daviddatuX25/Xentient/.planning/STATE.md

---
gsd_state_version: 1.0
milestone: v1.0
milestone_name: milestone
status: in_progress
last_updated: "2026-04-30T04:23:21.889Z"
progress:
  total_phases: 7
  completed_phases: 0
  total_plans: 0
  completed_plans: 0
---

# Project State: Xentient

## Project Reference

See: [.planning/PROJECT.md](file:///d:/Projects/Xentient/.planning/PROJECT.md) (updated 2026-04-19)

**Core value:** The IoT terminal — a thin voice/hardware bridge that lets any AI brain inhabit a physical room.
**Current focus:** Phase 8 (Web Console + Dashboard) COMPLETE — all 8 plans shipped. 203 tests passing, 0 TS errors. Dashboard served at localhost:3000 with Overview, Skill Manager, Telemetry, and Mode & Space panels.

## Active Context

Phase 1 (firmware), Phase 5 (docs), and Phase 6 (Xentient Layers) all complete. Platform Track P3 (ModeManager) and P4 (SpaceManager) built as part of Phase 6. CoreSkill types, SkillExecutor engine, SpaceManager, 8 MCP skill tools, observability notifications, core.ts wiring, and 34 Vitest tests — all committed and pushed.

Demo scope reduced: no furnished casing required — filming breadboard prototype as-is. P3-ASSY now covers breadboard assembly + validation only (no 3D-printed enclosure).

**Open bugs:** PIR wake not triggering ModeManager sleep→listen transition (9id, P0) — firmware ISR works, harness gap. Two P1 bugs deferred (bgx: dead MQTT sub, b94: audio prefix).

Quick task 260420-4do complete: ModeManager wired into Core runtime — MQTT mode/sensor events, idle timeouts (listen 60s, active 300s), PIR wake (sleep→listen), Pipeline mode-aware audio gating, LCD face display publishing on mode transitions.

## Milestone Status

| Milestone | Target Date | Status |
|---|---|---|
| V1 Prototype | 2026-04-24 | In Progress |

## Recent Decisions

- Bridge model adopted: Xentient = IoT terminal, not AI brain
- Three-tier architecture: Hardware / Core (Runtime + Web Control Panel) / AI Brain
- 4-layer doc system established (L0-L4)
- Phase 2 plans superseded by bridge reframe
- Two-track roadmap: Demo Track (frozen) + Platform Track (P1-P9)
- Brain Router: Core's dispatch layer routing handler calls across tiers
- Mem0 as primary memory layer (P2), Hermes as default brain (P1)
- Demo scope reduced: breadboard prototype filming, no furnished casing required
- P3-ASSY merged with 03-07: single hardware assembly task, breadboard scope only
- Phase 6 complete: CoreSkill types, SkillExecutor, SpaceManager, MCP tools, core wiring, 34 tests — all waves shipped
- Phase 7 planned: 6 gaps identified (G1-G6), 5 plans written (07-01 through 07-05), 5 design decisions locked
- Phase 1 confirmed complete: firmware (MQTT, LCD, mic, VAD, WS audio, camera relay, BME280, PIR ISR) all built and validated
- Platform Track P3/P4 already built as part of Phase 6 (ModeManager + SpaceManager)
- Roadmap + beads audited and aligned with actual project state
- Phase 8 added: Web Console + Dashboard — single-page HTML/JS dashboard served by ControlServer (NOT Laravel for v1), 8 plans (08-01 through 08-08)
- Phase 8 plan 07 complete: ControlServer refactored with MicroRouter route table, ControlServerDeps DI, 64KB body limit, static file fallthrough, SensorHistory ring buffer stub
- Phase 8 plan 01 complete: 16 REST endpoints (Skills 6, Packs 3, Spaces 2, Event Mappings 3, Sensor History 1, Config 1), PATCH allowlist, 409 conflict, 403 protected-delete, 32 tests
- PATCH allowlist: 9 patchable skill fields (enabled, displayName, trigger, actions, priority, cooldownMs, modeFilter, escalation, collect); forbidden: id, source, fireCount, escalationCount
- POST skill collision returns 409 (REST explicit), not MCP silent overwrite
- /api/skill-log path chosen over /api/skills/log to avoid :id route collision
- Phase 8 plan 02 complete: 10 new SSE event types (skill_registered/removed/updated, pack_loaded/unloaded, event_mapping_added/removed, sensor_update, counter_update, mode_change), throttled sensor broadcast (1s), counter interval lifecycle (Expansion 2.2), broadcastSkillEvent renamed to broadcastSSE
- mode_change emitted alongside modeChange (modeChange for EventBridge/SpaceManager internal, mode_change with timestamp for SSE dashboard)
- Counter interval optimization: starts on first skill with collect[], stops on last removal — no CPU waste when no collectors active
- Phase 8 plan 08 complete: 42 integration tests (REST API, SSE, error cases), ControlServer 400/413 bug fixes, toast/keyboard/responsive polish, SVG favicon
- ControlServer invalid JSON body now returns 400 (was 500)
- ControlServer oversized body now returns 413 cleanly (was socket error via req.destroy)
- Toast notifications: slide-in from right, 5s auto-dismiss, red left border for errors, role=alert
- Keyboard navigation: Tab/Enter/Space/Escape for skill table, Escape closes drawer
- Mobile responsive: bottom tab bar at <768px, 375px breakpoint for extra-small screens

## Roadmap Evolution

- Phase 5 added: Doc architecture refactor — restructure all docs to reflect bridge-model vision
- Phase 5 Plan 01 complete: VISION.md, NON_GOALS.md, HARDWARE.md, README.md created
- Phase 5 Plan 02 complete: CONTRACTS.md, PACKS.md, SPACES.md, INTEGRATIONS/*.md created
- Phase 5 Plan 03 complete: ROADMAP.md, PROJECT.md, REQUIREMENTS.md updated; NOTES.md trimmed; xentient.md shrunk; SUPERSEDED.md added

## Performance Metrics

| Phase | Plan | Duration | Tasks | Files |
|---|---|---|---|---|
| 05 | 01 | 15 min | 2 | 4 |
| 05 | 02 | 20 min | 2 | 7 |
| 05 | 03 | 10 min | 2 | 7 |
| 06 | 01-05 | ~3h | 5 waves | 10+ |
| 08 | 07 | 31min | 4 | 7 |
| 08 | 01 | 21min | 2 | 2 |
| 08 | 02 | 34min | 8 | 8 |
| 08 | 08 | 25min | 2 | 8 |

### Quick Tasks Completed

| # | Description | Date | Commit | Directory |
|---|---|---|---|---|
| 260419-abs | PlatformIO firmware scaffold — Node Base I2C enumeration | 2026-04-19 | a83bb7a | [260419-abs-platformio-node-base](.planning/quick/260419-abs-platformio-node-base/) |
| 260420-lcd | LCD 16x2 I2C driver — Core Face A output | 2026-04-20 | 13353b6 | [260420-lcd-lcd-core-face-a](.planning/quick/260420-lcd-lcd-core-face-a/) |
| 260420-mqtt | MQTT pub/sub client + JSON telemetry protocol | 2026-04-20 | 1f959ab | [260420-mqtt-pub-sub-client](.planning/quick/260420-mqtt-pub-sub-client/) |
| 260420-4do | Mode Manager wired into Core | 2026-04-20 | d21750b | [260420-4do-xentient-ifd](.planning/quick/260420-4do-xentient-ifd/) |

---
*State updated: 2026-04-28 (Phase 8 plan 08 complete. 42 integration tests. Wave 3 validation done.)*
