daviddatuX25/Xentient/.planning/phases/06-xentient-layers/06-02-PLAN.md

---
wave: 2
depends_on: 06-01-PLAN.md
files_modified:
  - harness/src/engine/SkillLog.ts
  - harness/src/engine/contextBuilders.ts
  - harness/src/engine/builtins.ts
  - harness/src/engine/SkillExecutor.ts
autonomous: true
requirements: [PT-03]
---

# Plan 06-02: SkillExecutor — Heartbeat Engine Core

## Goal
Build the `SkillExecutor` class that drives the Layer 1 tick loop: evaluates CoreSkills, executes FAST actions, fires escalations, and maintains the skill execution log.

## Prerequisites

> [!IMPORTANT]
> Run this before starting any tasks in this plan:
> ```bash
> cd harness
> npm install node-cron
> npm install -D @types/node-cron
> ```
> `node-cron` is **not** in `package.json` yet and is required by `SkillExecutor.ts`.

---

## Tasks

### Task 1: SkillLog (ring buffer)

<read_first>
- `harness/src/shared/types.ts` (SkillLogEntry, SKILL_LOG_CAPACITY from contracts.ts)
- `harness/src/shared/contracts.ts`
</read_first>

<action>
Create `harness/src/engine/SkillLog.ts`:

```typescript
import { SkillLogEntry } from '../shared/types';
import { SKILL_LOG_CAPACITY } from '../shared/contracts';

export class SkillLog {
  private entries: SkillLogEntry[] = [];
  private capacity: number;

  constructor(capacity = SKILL_LOG_CAPACITY) {
    this.capacity = capacity;
  }

  append(entry: SkillLogEntry): void {
    this.entries.push(entry);
    if (this.entries.length > this.capacity) {
      this.entries.shift();
    }
  }

  query(filter: {
    spaceId?: string;
    skillId?: string;
    since?: number;  // timestamp ms
    limit?: number;
  }): SkillLogEntry[] {
    let results = this.entries;
    if (filter.spaceId) results = results.filter(e => e.spaceId === filter.spaceId);
    if (filter.skillId) results = results.filter(e => e.skillId === filter.skillId);
    if (filter.since) results = results.filter(e => e.firedAt >= filter.since!);
    const limit = filter.limit ?? 100;
    return results.slice(-limit);
  }

  /** Attach Brain's escalation response to a log entry (matched by skillId + approximate firedAt) */
  attachEscalationResponse(skillId: string, firedAt: number, response: SkillLogEntry['escalationResponse']): void {
    const entry = [...this.entries].reverse().find(
      e => e.skillId === skillId && Math.abs(e.firedAt - firedAt) < 60_000
    );
    if (entry) entry.escalationResponse = response;
  }
}
```
</action>

<acceptance_criteria>
- `harness/src/engine/SkillLog.ts` exists with `class SkillLog`
- Contains `query(filter)` method
- Contains `attachEscalationResponse` method
- `cd harness && npx tsc --noEmit` exits 0
</acceptance_criteria>

---

### Task 2: Context Builders

<read_first>
- `harness/src/shared/types.ts` (ContextBuilderType)
- `harness/src/engine/ModeManager.ts`
</read_first>

<action>
Create `harness/src/engine/contextBuilders.ts`:

```typescript
import { ContextBuilderType, CoreSkill } from '../shared/types';

export interface SensorSnapshot {
  temperature?: number;
  humidity?: number;
  pressure?: number;
  motion?: boolean;
  lastMotionAt?: number;
}

export interface ContextPayload {
  skillId: string;
  spaceId: string;
  triggerData: Record<string, unknown>;
  sensors?: SensorSnapshot;
  cameraFrameB64?: string;    // base64 JPEG — populated by caller if available
  counters?: Record<string, number>;
  modeHistory?: string[];
}

export function buildContext(
  type: ContextBuilderType,
  skill: CoreSkill,
  triggerData: Record<string, unknown>,
  sensors: SensorSnapshot,
  counters: Record<string, number>,
  modeHistory: string[],
  getCameraFrame?: () => string | undefined,
): ContextPayload {
  const base: ContextPayload = {
    skillId: skill.id,
    spaceId: skill.spaceId,
    triggerData,
  };

  switch (type) {
    case 'minimal':
      return base;

    case 'sensor-snapshot':
      return { ...base, sensors };

    case 'camera-snapshot': {
      const frame = getCameraFrame?.();
      return { ...base, cameraFrameB64: frame };
    }

    case 'full-context':
      return {
        ...base,
        sensors,
        cameraFrameB64: getCameraFrame?.(),
        counters,
        modeHistory,
      };

    default:
      return base;
  }
}
```
</action>

<acceptance_criteria>
- `harness/src/engine/contextBuilders.ts` exists with `buildContext` function
- All 4 `ContextBuilderType` cases handled
- `cd harness && npx tsc --noEmit` exits 0
</acceptance_criteria>

---

### Task 3: Builtin CoreSkill definitions

<read_first>
- `harness/src/shared/types.ts` (CoreSkill, SkillTrigger, CoreAction)
- `harness/src/shared/contracts.ts` (BUILTIN_SKILL_IDS)
- `docs/SPEC-xentient-layers.md` §4.2 and §6.3
</read_first>

<action>
Create `harness/src/engine/builtins.ts`:

```typescript
import { CoreSkill } from '../shared/types';

/** PIR motion → wake from sleep to listen */
export const PIR_WAKE: CoreSkill = {
  id: '_pir-wake',
  displayName: 'PIR Wake',
  enabled: true,
  spaceId: '*',
  trigger: { type: 'event', event: 'motion_detected' },
  priority: 0,
  actions: [{ type: 'set_mode', mode: 'listen' }],
  source: 'builtin',
  cooldownMs: 0,
  fireCount: 0,
  escalationCount: 0,
};

/** Idle timer → return to sleep */
export const IDLE_SLEEP: CoreSkill = {
  id: '_idle-sleep',
  displayName: 'Idle Sleep',
  enabled: true,
  spaceId: '*',
  trigger: { type: 'interval', everyMs: 60_000 },  // check every 60s; condition on mode
  priority: 50,
  actions: [{ type: 'set_mode', mode: 'sleep' }],
  source: 'builtin',
  cooldownMs: 0,
  fireCount: 0,
  escalationCount: 0,
};

/** Sensor telemetry — log readings every 30s */
export const SENSOR_TELEMETRY: CoreSkill = {
  id: '_sensor-telemetry',
  displayName: 'Sensor Telemetry',
  enabled: true,
  spaceId: '*',
  trigger: { type: 'interval', everyMs: 30_000 },
  priority: 100,
  actions: [{ type: 'log', message: 'sensor-telemetry' }],
  source: 'builtin',
  cooldownMs: 0,
  fireCount: 0,
  escalationCount: 0,
};

/** Conflict arbiter — escalates skill conflicts to Brain */
export const DETERMINE_SKILL: CoreSkill = {
  id: '_determine-skill',
  displayName: 'Skill Conflict Arbitrator',
  enabled: true,
  spaceId: '*',
  trigger: { type: 'internal', event: 'skill_conflict' },
  priority: 0,
  actions: [],
  escalation: {
    conditions: [{ field: 'conflictCount', operator: '>=', value: 2 }],
    event: 'skill_conflict',
    contextBuilder: 'full-context',
    priority: 'urgent',
    cooldownMs: 0,
  },
  source: 'builtin',
  cooldownMs: 0,
  fireCount: 0,
  escalationCount: 0,
};

export const ALL_BUILTINS: CoreSkill[] = [PIR_WAKE, IDLE_SLEEP, SENSOR_TELEMETRY, DETERMINE_SKILL];
```
</action>

<acceptance_criteria>
- `harness/src/engine/builtins.ts` exists with all 4 builtin definitions
- `ALL_BUILTINS` array exported with 4 entries
- `_determine-skill` has `escalation.event === 'skill_conflict'`
- `cd harness && npx tsc --noEmit` exits 0
</acceptance_criteria>

---

### Task 4: SkillExecutor class

<read_first>
- `harness/src/shared/types.ts` (CoreSkill, CoreAction, EscalationCondition)
- `harness/src/shared/contracts.ts` (SKILL_EVENTS, CONFLICT_TIMEOUT_MS, BUILTIN_SKILL_IDS)
- `harness/src/engine/ModeManager.ts` (getMode, setMode signatures)
- `harness/src/engine/SkillLog.ts`
- `harness/src/engine/contextBuilders.ts`
- `harness/src/engine/builtins.ts`
- `harness/src/mcp/events.ts` (how notifications are sent today)
- `docs/SPEC-xentient-layers.md` §4, §5, §6
</read_first>

<action>
Create `harness/src/engine/SkillExecutor.ts`:

```typescript
import { EventEmitter } from 'events';
import pino from 'pino';
import cron from 'node-cron';
import { McpServer } from '@modelcontextprotocol/sdk/server/mcp.js';
import {
  CoreSkill, CoreAction, EscalationCondition, SkillLogEntry,
  SkillFireEvent, SkillEscalationEvent, SkillConflictEvent,
  ConflictResolution, PendingConflict, ObservabilityEvent,
} from '../shared/types';
import { SKILL_EVENTS, BUILTIN_SKILL_IDS, CONFLICT_TIMEOUT_MS } from '../shared/contracts';
import { ModeManager } from './ModeManager';
import { MqttClient } from '../comms/MqttClient';
import { SkillLog } from './SkillLog';
import { buildContext, SensorSnapshot } from './contextBuilders';
import { ALL_BUILTINS } from './builtins';

const logger = pino({ name: 'skill-executor' });

export interface SkillExecutorOptions {
  spaceId: string;
  tickMs?: number;
  modeManager: ModeManager;
  mqttClient: MqttClient;
  mcpServer: McpServer;
  skillLog: SkillLog;
  getSensorSnapshot: () => SensorSnapshot;
  getCameraFrame?: () => string | undefined;
  onObservabilityEvent: (event: ObservabilityEvent) => void;
}

export class SkillExecutor extends EventEmitter {
  private skills: Map<string, CoreSkill> = new Map();
  private counters: Map<string, number> = new Map();
  private modeHistory: string[] = [];
  private cronHandles: Map<string, cron.ScheduledTask> = new Map();
  private intervalHandles: Map<string, NodeJS.Timeout> = new Map();
  private pendingConflicts: Map<string, PendingConflict> = new Map();
  private tickHandle: NodeJS.Timeout | null = null;
  private opts: SkillExecutorOptions;
  private activeMode: string = 'default';

  constructor(opts: SkillExecutorOptions) {
    super();
    this.opts = opts;
    // Register all builtins
    for (const builtin of ALL_BUILTINS) {
      this.skills.set(builtin.id, { ...builtin });
    }
  }

  // ---- Lifecycle ----

  start(): void {
    this.tickHandle = setInterval(() => this.tick(), this.opts.tickMs ?? 5000);
    this.setupScheduledSkills();
    logger.info({ spaceId: this.opts.spaceId }, 'SkillExecutor started');
  }

  stop(): void {
    if (this.tickHandle) clearInterval(this.tickHandle);
    for (const [, task] of this.cronHandles) task.stop();
    for (const [, handle] of this.intervalHandles) clearInterval(handle);
    this.cronHandles.clear();
    this.intervalHandles.clear();
    logger.info({ spaceId: this.opts.spaceId }, 'SkillExecutor stopped');
  }

  // ---- Mode ----

  switchMode(newMode: string): void {
    const prev = this.activeMode;
    this.activeMode = newMode;
    this.modeHistory.push(newMode);
    if (this.modeHistory.length > 20) this.modeHistory.shift();
    logger.info({ spaceId: this.opts.spaceId, prev, newMode }, 'Behavioral mode switched');
  }

  getMode(): string { return this.activeMode; }

  // ---- Skill registry ----

  registerSkill(skill: CoreSkill): void {
    this.skills.set(skill.id, { ...skill, fireCount: 0, escalationCount: 0 });
    // Wire up cron/interval triggers immediately
    this.setupSkillSchedule(skill);
    logger.info({ skillId: skill.id }, 'Skill registered');
  }

  updateSkill(id: string, patch: Partial<CoreSkill>): boolean {
    const existing = this.skills.get(id);
    if (!existing) return false;
    const updated = { ...existing, ...patch };
    this.skills.set(id, updated);
    // Re-wire schedule if trigger changed
    this.teardownSkillSchedule(id);
    this.setupSkillSchedule(updated);
    return true;
  }

  disableSkill(id: string, enabled: boolean): boolean {
    const skill = this.skills.get(id);
    if (!skill) return false;
    skill.enabled = enabled;
    return true;
  }

  removeSkill(id: string): boolean {
    if ((BUILTIN_SKILL_IDS as readonly string[]).includes(id)) {
      logger.warn({ id }, 'Cannot remove builtin skill');
      return false;
    }
    this.teardownSkillSchedule(id);
    return this.skills.delete(id);
  }

  listSkills(spaceId?: string): CoreSkill[] {
    const all = Array.from(this.skills.values());
    if (!spaceId) return all;
    return all.filter(s => s.spaceId === spaceId || s.spaceId === '*');
  }

  // ---- Event-triggered skills (from MQTT/MCP notifications) ----

  handleEvent(eventName: string, triggerData: Record<string, unknown> = {}): void {
    const matching = Array.from(this.skills.values()).filter(s =>
      s.enabled &&
      this.matchesSpace(s) &&
      s.trigger.type === 'event' &&
      (s.trigger as { type: 'event'; event: string }).event === eventName
    );
    if (matching.length > 0) {
      this.executeSkillSet(matching, { type: 'event', event: eventName }, triggerData);
    }
  }

  // ---- Conflict resolution (Brain's answer) ----

  resolveConflict(resolution: ConflictResolution & { conflictGroup: string }): void {
    const pending = this.pendingConflicts.get(resolution.conflictGroup);
    if (!pending) return;
    clearTimeout(pending.timeoutHandle);
    this.pendingConflicts.delete(resolution.conflictGroup);

    for (const skillId of resolution.execute) {
      const skill = this.skills.get(skillId);
      if (skill) this.executeL1Actions(skill, pending.triggerData);
    }
    logger.info({ resolution }, 'Conflict resolved by Brain');
  }

  // ---- Private: tick loop ----

  private tick(): void {
    const now = Date.now();
    const sensors = this.opts.getSensorSnapshot();
    const ctx = { mode: this.opts.modeManager.getMode(), sensors, now };

    const candidates: CoreSkill[] = [];
    for (const skill of this.skills.values()) {
      if (!skill.enabled) continue;
      if (!this.matchesSpace(skill)) continue;
      if (skill.trigger.type !== 'sensor') continue; // sensor triggers evaluated on tick; cron/interval handled by schedule
      // Note: cooldown is checked inside fireSkill() — no need to check here
      if (this.evaluateTrigger(skill.trigger, ctx)) candidates.push(skill);
    }

    if (candidates.length > 0) {
      this.executeSkillSet(candidates, { type: 'tick' } as any, {});
    }
  }

  // ---- Private: schedule wiring ----

  private setupScheduledSkills(): void {
    for (const skill of this.skills.values()) {
      this.setupSkillSchedule(skill);
    }
  }

  private setupSkillSchedule(skill: CoreSkill): void {
    if (skill.trigger.type === 'cron') {
      const task = cron.schedule(skill.trigger.schedule, () => {
        if (!skill.enabled || !this.matchesSpace(skill)) return;
        this.executeSkillSet([skill], skill.trigger, {});
      });
      this.cronHandles.set(skill.id, task);
    } else if (skill.trigger.type === 'interval') {
      const handle = setInterval(() => {
        if (!skill.enabled || !this.matchesSpace(skill)) return;
        const now = Date.now();
        if (skill.cooldownMs && skill.lastFiredAt && (now - skill.lastFiredAt < skill.cooldownMs)) return;
        this.executeSkillSet([skill], skill.trigger, {});
      }, skill.trigger.everyMs);
      this.intervalHandles.set(skill.id, handle);
    }
  }

  private teardownSkillSchedule(id: string): void {
    this.cronHandles.get(id)?.stop();
    this.cronHandles.delete(id);
    const h = this.intervalHandles.get(id);
    if (h) clearInterval(h);
    this.intervalHandles.delete(id);
  }

  // ---- Private: execution ----

  private executeSkillSet(skills: CoreSkill[], trigger: any, triggerData: Record<string, unknown>): void {
    // Group by conflictGroup, check for conflicts
    const byGroup = new Map<string, CoreSkill[]>();
    const noGroup: CoreSkill[] = [];

    for (const skill of skills) {
      if (skill.escalation?.conflictGroup) {
        const g = skill.escalation.conflictGroup;
        if (!byGroup.has(g)) byGroup.set(g, []);
        byGroup.get(g)!.push(skill);
      } else {
        noGroup.push(skill);
      }
    }

    // Execute non-conflicting skills directly
    for (const skill of noGroup) {
      this.fireSkill(skill, triggerData);
    }

    // Handle conflict groups
    for (const [group, groupSkills] of byGroup) {
      if (groupSkills.length === 1) {
        this.fireSkill(groupSkills[0], triggerData);
      } else {
        this.handleConflict(group, groupSkills, triggerData);
      }
    }
  }

  private fireSkill(skill: CoreSkill, triggerData: Record<string, unknown>): void {
    const now = Date.now();

    // Cooldown check — applies to ALL trigger paths (tick, event, cron, interval)
    // Moved here from tick() so event-triggered skills also respect cooldown.
    if (skill.cooldownMs && skill.lastFiredAt && (now - skill.lastFiredAt < skill.cooldownMs)) {
      logger.debug({ skillId: skill.id, remainingMs: skill.cooldownMs - (now - skill.lastFiredAt) }, 'Skill skipped (cooldown)');
      return;
    }

    skill.lastFiredAt = now;
    skill.fireCount++;

    const actionsExecuted = this.executeL1Actions(skill, triggerData);
    const shouldEscalate = this.checkEscalation(skill, triggerData);

    const logEntry: SkillLogEntry = {
      skillId: skill.id,
      spaceId: this.opts.spaceId,
      mode: this.activeMode,
      firedAt: now,
      triggerData,
      actionsExecuted,
      escalated: shouldEscalate,
    };
    this.opts.skillLog.append(logEntry);

    const event: SkillFireEvent = {
      type: 'skill_fired',
      skillId: skill.id,
      spaceId: this.opts.spaceId,
      mode: this.activeMode,
      trigger: skill.trigger.type,
      actionsExecuted,
      escalated: shouldEscalate,
      timestamp: now,
    };
    this.opts.onObservabilityEvent(event);

    if (shouldEscalate) this.escalate(skill, triggerData, now);
  }

  private executeL1Actions(skill: CoreSkill, triggerData: Record<string, unknown>): string[] {
    const executed: string[] = [];
    for (const action of skill.actions) {
      try {
        this.runAction(action, triggerData);
        executed.push(action.type);
      } catch (err) {
        logger.error({ err, action, skillId: skill.id }, 'L1 action error');
      }
    }
    return executed;
  }

  private runAction(action: CoreAction, _triggerData: Record<string, unknown>): void {
    const { modeManager, mqttClient } = this.opts;
    switch (action.type) {
      case 'set_mode':
        modeManager.setMode(action.mode);
        break;
      case 'set_lcd':
        // Emit to MCP tools layer — resolved via Core's tool handler
        this.emit('lcd', { line1: action.line1, line2: action.line2 });
        break;
      case 'play_chime':
        this.emit('chime', { preset: action.preset });
        break;
      case 'mqtt_publish':
        // Fix #2: MqttClient exposes publish(), NOT sendCommand()
        mqttClient.publish(action.topic, action.payload);
        break;
      case 'increment_counter': {
        const cur = this.counters.get(action.name) ?? 0;
        this.counters.set(action.name, cur + 1);
        break;
      }
      case 'log':
        logger.info({ message: action.message, spaceId: this.opts.spaceId }, 'Skill log action');
        break;
    }
  }

  private checkEscalation(skill: CoreSkill, triggerData: Record<string, unknown>): boolean {
    if (!skill.escalation) return false;
    const { conditions, cooldownMs } = skill.escalation;
    const now = Date.now();
    if (cooldownMs && skill.lastEscalatedAt && (now - skill.lastEscalatedAt < cooldownMs)) return false;

    return conditions.every(cond => {
      const val = this.resolveConditionField(cond.field, triggerData);
      return this.compare(val, cond.operator, cond.value);
    });
  }

  private escalate(skill: CoreSkill, triggerData: Record<string, unknown>, firedAt: number): void {
    const { mcpServer, getSensorSnapshot, getCameraFrame } = this.opts;
    skill.lastEscalatedAt = firedAt;
    skill.escalationCount++;

    const context = buildContext(
      skill.escalation!.contextBuilder,
      skill,
      triggerData,
      getSensorSnapshot(),
      Object.fromEntries(this.counters),
      this.modeHistory,
      getCameraFrame,
    );

    const event: SkillEscalationEvent = {
      type: 'skill_escalated',
      skillId: skill.id,
      spaceId: this.opts.spaceId,
      event: skill.escalation!.event,
      priority: skill.escalation!.priority,
      brainConnected: true, // TODO: check HealthMonitor
      timestamp: firedAt,
    };
    this.opts.onObservabilityEvent(event);

    // Fix #6: Use mcpServer.notification() (high-level Promise-returning API)
    // NOT mcpServer.server.notification() (low-level raw Server method)
    mcpServer.notification({
      method: SKILL_EVENTS.SKILL_ESCALATED,
      params: {
        skillId: skill.id,
        spaceId: this.opts.spaceId,
        event: skill.escalation!.event,
        context,
        priority: skill.escalation!.priority,
      },
    }).catch((err: Error) => logger.error({ err, skillId: skill.id }, 'Failed to send skill_escalated notification'));

    logger.info({ skillId: skill.id, spaceId: this.opts.spaceId }, 'Skill escalated to Brain');
  }

  private handleConflict(group: string, skills: CoreSkill[], triggerData: Record<string, unknown>): void {
    const now = Date.now();
    logger.warn({ group, skills: skills.map(s => s.id) }, 'Skill conflict detected');

    const conflictEvent: SkillConflictEvent = {
      type: 'skill_conflict',
      conflictingSkills: skills.map(s => s.id),
      spaceId: this.opts.spaceId,
      resolution: 'pending',
      timestamp: now,
    };
    this.opts.onObservabilityEvent(conflictEvent);

    // Try Brain arbitration (Tier 2)
    const timeoutHandle = setTimeout(() => {
      // Fallback: priority ordering (Tier 1)
      logger.warn({ group }, 'Conflict timeout — falling back to priority ordering');
      this.pendingConflicts.delete(group);
      const sorted = skills.sort((a, b) => a.priority - b.priority);
      this.fireSkill(sorted[0], triggerData);
    }, CONFLICT_TIMEOUT_MS);

    this.pendingConflicts.set(group, {
      conflictingSkills: skills.map(s => s.id),
      spaceId: this.opts.spaceId,
      triggerData,
      startedAt: now,
      timeoutHandle,
    });

    // Fix #6: Use mcpServer.notification() (high-level Promise-returning API)
    this.opts.mcpServer.notification({
      method: SKILL_EVENTS.SKILL_CONFLICT,
      params: {
        conflictingSkills: skills.map(s => s.id),
        spaceId: this.opts.spaceId,
        triggerData,
        conflictGroup: group,
      },
    }).catch((err: Error) => logger.error({ err, group }, 'Failed to send skill_conflict notification'));
  }

  // ---- Private: helpers ----

  private matchesSpace(skill: CoreSkill): boolean {
    return skill.spaceId === '*' || skill.spaceId === this.opts.spaceId;
  }

  private evaluateTrigger(trigger: any, ctx: any): boolean {
    if (trigger.type === 'sensor') {
      const val = ctx.sensors[trigger.sensor as string] ?? 0;
      return this.compare(val, trigger.operator, trigger.value);
    }
    return false; // cron/interval handled via schedule, event via handleEvent
  }

  private resolveConditionField(field: string, triggerData: Record<string, unknown>): number {
    if (triggerData[field] !== undefined) return Number(triggerData[field]);
    return this.counters.get(field) ?? 0;
  }

  private compare(actual: number, op: string, expected: number): boolean {
    switch (op) {
      case '>': return actual > expected;
      case '<': return actual < expected;
      case '>=': return actual >= expected;
      case '<=': return actual <= expected;
      case '==': return actual === expected;
      case '!=': return actual !== expected;
      default: return false;
    }
  }
}
```
</action>

<acceptance_criteria>
- `harness/src/engine/SkillExecutor.ts` exists with `class SkillExecutor extends EventEmitter`
- Contains `registerSkill`, `updateSkill`, `disableSkill`, `removeSkill`, `listSkills` methods
- Contains `handleEvent` method for event-triggered skills
- Contains `resolveConflict` method
- Contains `start()` and `stop()` lifecycle methods
- Builtin skills registered in constructor via `ALL_BUILTINS`
- `cd harness && npx tsc --noEmit` exits 0
</acceptance_criteria>

---

## Verification

```bash
cd harness && npx tsc --noEmit
```

<must_haves>
- SkillLog ring buffer with query + attachEscalationResponse
- SkillExecutor with full tick loop, L1 action execution, escalation pipeline, conflict handling
- Builtin skills defined and registered automatically
- Context builders for all 4 ContextBuilderType values
- TypeScript compiles clean
</must_haves>
