daviddatuX25/Xentient/.planning/phases/06-xentient-layers/06-04-PLAN.md

---
wave: 4
depends_on: 06-03-PLAN.md
files_modified:
  - harness/src/core.ts
autonomous: true
requirements: [PT-03, PT-04]
---

# Plan 06-04: Wire SpaceManager into Core + Default Space Bootstrap

## Goal
Update `core.ts` to instantiate `SpaceManager`, create the default Space on startup, forward MQTT events to skill execution, and pipe observability events to the `ControlServer` SSE stream.

---

## Tasks

### Task 1: Audit core.ts startup sequence

<read_first>
- `harness/src/core.ts` (full file — understand ALL existing wiring)
- `harness/src/engine/SpaceManager.ts`
- `harness/src/engine/ModeManager.ts`
- `harness/src/mcp/tools.ts` (registerTools signature now takes SpaceManager)
- `harness/src/mcp/server.ts`
</read_first>

<action>
Read `harness/src/core.ts` fully before making any changes. Identify:
1. Where `ModeManager` is instantiated — SpaceManager is wired right after
2. Where `registerTools(server, ...)` is called — add `spaceManager` argument
3. Where MQTT events are handled (`mqtt.on('vad', ...)`, `mqtt.on('motion', ...)`) — forward to SpaceManager
4. Where the `ControlServer` SSE push happens — add observability event relay
</action>

<acceptance_criteria>
- This task is a READ task. No file changes. Output: list of line numbers for ModeManager init, registerTools call, and MQTT event handlers in core.ts.
</acceptance_criteria>

---

### Task 2: Instantiate SpaceManager and default Space

<read_first>
- `harness/src/core.ts` (audit from Task 1)
- `harness/src/engine/SpaceManager.ts`
- `harness/src/shared/types.ts` (Space interface)
- `harness/config/default.json` (NODE_ID config)
</read_first>

<action>
In `harness/src/core.ts`, after the `ModeManager` instantiation, add:

```typescript
import { SpaceManager } from './engine/SpaceManager';
import { Space } from './shared/types';

// --- SpaceManager (Xentient Layers) ---
const spaceManager = new SpaceManager(
  mcpServer,
  modeManager,
  mqtt,
  // Fix #7: sensorCache is a plain object literal, NOT a class with methods.
  // Spread it to return a snapshot clone — do NOT call .snapshot().
  () => ({ ...sensorCache }),
  () => cameraServer.getLatestJpeg?.()?.toString('base64'), // getCameraFrame — optional
);

// Default Space (single-node v1)
const defaultSpace: Space = {
  id: 'default',
  nodeBaseId: config.nodeId ?? 'node-01',
  activePack: 'default',
  spaceMode: modeManager.getMode(),
  activeMode: 'default',
  integrations: [],
  sensors: ['temperature', 'humidity', 'motion'],
};
spaceManager.addSpace(defaultSpace);
logger.info({ spaceId: defaultSpace.id }, 'Default space initialized');
```

**Note:** `sensorCache` is declared as a plain object literal in `core.ts` (`const sensorCache: SensorCache = { ... }`). It has no methods. Use `() => ({ ...sensorCache })` to pass a snapshot factory.
</action>

<acceptance_criteria>
- `harness/src/core.ts` imports `SpaceManager` from `'./engine/SpaceManager'`
- `harness/src/core.ts` contains `spaceManager.addSpace(defaultSpace)`
- `harness/src/core.ts` contains `const defaultSpace: Space = {`
- `cd harness && npx tsc --noEmit` exits 0
</acceptance_criteria>

---

### Task 3: Pass SpaceManager to registerTools

<read_first>
- `harness/src/core.ts` (locate registerTools call)
- `harness/src/mcp/tools.ts` (updated signature)
</read_first>

<action>
Find the `startMcpServer({...})` call in `core.ts`. Update it to pass `spaceManager`:

```typescript
// Before:
const mcpServer = await startMcpServer({
  mqtt,
  audio: audioServer,
  camera: cameraServer,
  modeManager,
  sensorCache,
});

// After (Fix #5 — McpToolDeps now includes spaceManager):
const mcpServer = await startMcpServer({
  mqtt,
  audio: audioServer,
  camera: cameraServer,
  modeManager,
  sensorCache,
  spaceManager,  // NEW — enables the 8 skill management MCP tools
});
```

**Important ordering note:** `SpaceManager` constructor requires `mcpServer`, but `startMcpServer()` returns `mcpServer`. This creates a circular dependency. Resolve by:
1. Calling `startMcpServer()` first WITHOUT `spaceManager`
2. Instantiating `SpaceManager` after, passing the returned `mcpServer`
3. Then calling `mcpServer.addTool(...)` for the 8 new skill tools — OR, restructure server.ts to accept a late-bound `spaceManager` setter

The cleanest solution: add a `spaceManager` setter on the MCP server or pass `spaceManager` as a lazy ref:
```typescript
// Option A: inject via setter after both are created
const mcpServer = await startMcpServer({ mqtt, audio: audioServer, camera: cameraServer, modeManager, sensorCache });
const spaceManager = new SpaceManager(mcpServer, modeManager, mqtt, () => ({ ...sensorCache }));
mcpServer.setSpaceManager(spaceManager);  // adds the 8 skill tools dynamically

// Option B (simpler for v1): use a mutable ref
const spaceManagerRef = { current: null as SpaceManager | null };
const mcpServer = await startMcpServer({ ..., spaceManagerRef });
// then: spaceManagerRef.current = new SpaceManager(mcpServer, ...);
```
Choose Option A or B during implementation — document the choice in a comment.
</action>

<acceptance_criteria>
- `harness/src/core.ts` `registerTools` call includes `spaceManager`
- `cd harness && npx tsc --noEmit` exits 0
</acceptance_criteria>

---

### Task 4: Forward MQTT events to SkillExecutor

<read_first>
- `harness/src/core.ts` (MQTT event handler section)
- `harness/src/comms/MqttClient.ts` (event names emitted: 'vad', 'sensor', 'heartbeat', 'cameraFrame')
- `harness/src/engine/SpaceManager.ts` (handleEvent method)
</read_first>

<action>
In `core.ts`, after the existing MQTT event handlers, add forwarding to SpaceManager.

**Important:** MqttClient does NOT emit `'motion'` or `'vad'` events. Check `comms/MqttClient.ts` `handleMessage()` for the real event names. The actual events are:
- PIR motion → arrives via `mqtt.on('sensor', ...)` where `data.peripheralType === PERIPHERAL_IDS.PIR`
- VAD triggers → arrive via `mqtt.on('triggerPipeline', ...)` where `data.source === 'voice'`

```typescript
// Forward PIR motion to SkillExecutor event-triggered skills
mqtt.on('sensor', (data: unknown) => {
  const d = data as { peripheralType?: number; payload?: { motion?: boolean } };
  if (d.peripheralType === PERIPHERAL_IDS.PIR && d.payload?.motion) {
    spaceManager.handleEvent('*', 'motion_detected', { nodeId: mqtt.nodeId, timestamp: Date.now() });
  }
  // BME280 sensor update — forward for sensor-triggered skills
  if (d.peripheralType === PERIPHERAL_IDS.BME280) {
    spaceManager.handleEvent('*', 'sensor_update', { payload: d.payload, timestamp: Date.now() });
  }
});

// Forward VAD voice events to SkillExecutor
mqtt.on('triggerPipeline', (data: unknown) => {
  const d = data as { source?: string; stage?: string };
  if (d.source === 'voice') {
    const eventName = d.stage === 'start' ? 'voice_start' : 'voice_end';
    spaceManager.handleEvent('*', eventName, { timestamp: Date.now() });
  }
});

// Keep SpaceMode in sync when ModeManager transitions hardware state
modeManager.on('modeChange', ({ from, to }) => {
  spaceManager.updateSpaceMode('default', to);
  logger.info({ from, to }, 'SpaceMode synced with ModeManager');
});
```

**Note:** The existing `mqtt.on('sensor', ...)` in `events.ts` handles sensorCache updates. Add `spaceManager.handleEvent()` calls to the same handler — do NOT duplicate the handler, instead augment the existing one.
</action>

<acceptance_criteria>
- `harness/src/core.ts` contains `spaceManager.handleEvent('motion_detected'`
- `harness/src/core.ts` contains `spaceManager.handleEvent('voice_start'`
- `cd harness && npx tsc --noEmit` exits 0
</acceptance_criteria>

---

### Task 5: Relay observability events to ControlServer SSE

<read_first>
- `harness/src/core.ts`
- `harness/src/comms/ControlServer.ts` (how SSE events are pushed today — find the push method)
</read_first>

<action>
Find how `ControlServer` pushes SSE events. Looking at `ControlServer.ts`, it exposes a private `broadcastSSE(data: object): void` method. This needs to be made accessible from outside, OR the relay can use the pattern already established (MQTT → SSE).

After `spaceManager.addSpace(defaultSpace)`, add:

```typescript
// Relay SkillExecutor observability events to Web Dashboard via SSE
// SpaceManager extends EventEmitter — wire events to ControlServer's broadcastSSE
// Note: broadcastSSE is currently private. Either:
//   (a) Add a public sendSkillEvent(event) method to ControlServer, OR
//   (b) Make broadcastSSE protected and extend, OR
//   (c) Expose a public emit method that wraps broadcastSSE
// Simplest for v1: add a public broadcastSkillEvent() method to ControlServer during this task:
spaceManager.on('skill_fired', (event: any) => {
  controlServer.broadcastSkillEvent({ type: 'skill_fired', ...event });
});
spaceManager.on('skill_escalated', (event: any) => {
  controlServer.broadcastSkillEvent({ type: 'skill_escalated', ...event });
});
spaceManager.on('skill_conflict', (event: any) => {
  controlServer.broadcastSkillEvent({ type: 'skill_conflict', ...event });
});
```

Add a `broadcastSkillEvent(data: object): void` public method to `ControlServer.ts` that delegates to `this.broadcastSSE(data)`.

**Important:** `SpaceManager` extends `EventEmitter` (fixed in Plan 06-03 Task 1) — `this.emit()` works correctly.
</action>

<acceptance_criteria>
- `harness/src/core.ts` contains `spaceManager.on?.('skill_fired'`
- `harness/src/engine/SpaceManager.ts` extends `EventEmitter` (or has observable pattern)
- `cd harness && npx tsc --noEmit` exits 0
</acceptance_criteria>

---

### Task 6: Graceful shutdown

<read_first>
- `harness/src/core.ts` (process.on('SIGINT'/'SIGTERM') handler if exists, or index.ts)
- `harness/src/index.ts`
</read_first>

<action>
In the shutdown/cleanup section of `core.ts` or `index.ts`, add:

```typescript
spaceManager.stopAll();
logger.info('SpaceManager stopped — all SkillExecutors shut down');
```

This must be called before `process.exit()` or in the `SIGINT`/`SIGTERM` handler.
</action>

<acceptance_criteria>
- `harness/src/core.ts` or `harness/src/index.ts` contains `spaceManager.stopAll()`
- `cd harness && npx tsc --noEmit` exits 0
</acceptance_criteria>

---

## Verification

```bash
cd harness && npx tsc --noEmit
# Then start and check logs:
cd harness && npm run dev
# Expected log lines:
# INFO  skill-executor  SkillExecutor started  {"spaceId":"default"}
# INFO  space-manager   Default space initialized  {"spaceId":"default"}
```

<must_haves>
- SpaceManager instantiated in core.ts with default Space
- SpaceManager passed to registerTools (8 new MCP tools now exposed)
- MQTT events forwarded to SpaceManager.handleEvent
- SkillExecutor starts and logs "SkillExecutor started"
- Graceful shutdown calls spaceManager.stopAll()
- TypeScript compiles clean
</must_haves>
