daviddatuX25/Xentient/.planning/phases/07-skill-engine-hardening/07-01-PLAN.md

---
wave: 1
depends_on: none
files_modified:
  - harness/src/engine/SkillExecutor.ts
  - harness/src/engine/builtins.ts
  - harness/src/engine/SpaceManager.ts
  - harness/src/shared/types.ts
  - harness/src/shared/contracts.ts
autonomous: true
requirements: [PT-03, PT-04]
---

# Plan 07-01: Gap Fixes — Wire Mode Triggers, Composite Evaluation, modeFilter, Remove _idle-sleep, DataCollector

## Goal
Close Phase 6 gaps G1–G5: make declared trigger types actually fire, enforce modeFilter, remove the idle-sleep conflict, and implement DataCollector auto-collect/reset.

---

## Tasks

### Task 1: Wire mode trigger evaluation (G1)

<read_first>
- `harness/src/engine/SkillExecutor.ts` (lines 114-124 — `handleEvent`)
- `harness/src/core.ts` (lines 161-164 — modeChange forwarding)
- `harness/src/shared/types.ts` (SkillTrigger type union)
</read_first>

<action>
1. In `SkillExecutor.ts`, update `handleEvent()` to also match `{ type: 'mode' }` triggers:

```typescript
handleEvent(eventName: string, triggerData: Record<string, unknown> = {}): void {
  const matching = Array.from(this.skills.values()).filter(s => {
    if (!s.enabled || !this.matchesSpace(s)) return false;
    if (s.trigger.type === 'event') {
      return (s.trigger as { type: 'event'; event: string }).event === eventName;
    }
    if (s.trigger.type === 'mode') {
      const mt = s.trigger as { type: 'mode'; from: string; to: string };
      if (eventName !== 'mode_transition') return false;
      const from = triggerData.from as string;
      const to = triggerData.to as string;
      const fromMatch = mt.from === '*' || mt.from === from;
      const toMatch = mt.to === '*' || mt.to === to;
      return fromMatch && toMatch;
    }
    return false;
  });
  if (matching.length > 0) {
    this.executeSkillSet(matching, { type: 'mode' }, triggerData);
  }
}
```

2. In `core.ts`, update the `modeManager.on('modeChange')` handler to forward mode transitions as events AND sync SpaceMode separately:

```typescript
// Replace lines 161-164 with:
modeManager.on("modeChange", ({ from, to }) => {
  // Forward SpaceMode transition as skill event (G1 fix)
  spaceManager.handleEvent('mode_transition', { from, to, timestamp: Date.now() });
  // Sync hardware mode on the Space object
  spaceManager.updateSpaceMode('default', to);
  logger.info({ from, to }, 'SpaceMode synced with ModeManager');
});
```

3. Add `updateSpaceMode(spaceId: string, mode: string)` method to `SpaceManager` that updates the Space's `spaceMode` field:

```typescript
/** Sync the Space's hardware mode (SpaceMode) from ModeManager.
 *  This is separate from BehavioralMode (which is a skill filter, not hardware state).
 *  Do NOT call executor.switchMode() here — that's for behavioral mode changes via MCP. */
updateSpaceMode(spaceId: string, mode: string): void {
  const space = this.spaces.get(spaceId);
  if (!space) {
    logger.warn({ spaceId }, 'updateSpaceMode: unknown space');
    return;
  }
  const prev = space.spaceMode;
  space.spaceMode = mode as Mode;
  if (prev !== mode) {
    this.emit('spaceModeChanged', { spaceId, from: prev, to: mode });
  }
}
```
</action>

<acceptance_criteria>
- A skill with `trigger: { type: 'mode', from: 'sleep', to: 'listen' }` fires when ModeManager transitions from sleep to listen
- `handleEvent('mode_transition', { from: 'sleep', to: 'listen' })` matches the trigger
- Wildcard `from: '*'` or `to: '*'` matches any transition
- `core.ts` no longer conflates SpaceMode with BehavioralMode in `switchMode`
</acceptance_criteria>

---

### Task 2: Add composite trigger evaluation (G2)

<read_first>
- `harness/src/engine/SkillExecutor.ts` (lines 387-393 — `evaluateTrigger`)
- `harness/src/shared/types.ts` (SkillTrigger composite type)
</read_first>

<action>
Update `evaluateTrigger()` to handle `composite` triggers with recursive evaluation:

```typescript
private evaluateTrigger(trigger: Record<string, unknown>, ctx: Record<string, unknown>): boolean {
  if (trigger.type === 'sensor') {
    const val = (ctx.sensors as Record<string, unknown>)?.[trigger.sensor as string] as number ?? 0;
    return this.compare(val, trigger.operator as string, trigger.value as number);
  }
  if (trigger.type === 'composite') {
    const subTriggers = trigger.all as Record<string, unknown>[];
    if (!subTriggers || subTriggers.length === 0) return false;
    // Depth limit to prevent infinite recursion
    const depth = (ctx._compositeDepth as number) ?? 0;
    if (depth > 5) {
      logger.warn({ skillId: ctx._skillId }, 'Composite trigger depth limit exceeded');
      return false;
    }
    return subTriggers.every(sub => this.evaluateTrigger(sub, { ...ctx, _compositeDepth: depth + 1 }));
  }
  return false;
}
```

Also update `tick()` to pass skill ID in context for debugging:

```typescript
private tick(): void {
  const sensors = this.opts.getSensorSnapshot();
  const ctx = { mode: this.opts.modeManager.getMode(), sensors, now: Date.now() };
  const candidates: CoreSkill[] = [];
  for (const skill of this.skills.values()) {
    if (!skill.enabled || !this.matchesSpace(skill)) continue;
    if (skill.trigger.type === 'sensor') {
      if (this.evaluateTrigger(skill.trigger as unknown as Record<string, unknown>, { ...ctx, _skillId: skill.id })) candidates.push(skill);
    }
  }
  if (candidates.length > 0) {
    this.executeSkillSet(candidates, { type: 'tick' } as Record<string, unknown>, {});
  }
}
```
</action>

<acceptance_criteria>
- A skill with `trigger: { type: 'composite', all: [{ type: 'sensor', sensor: 'temperature', operator: '>', value: 30 }, { type: 'sensor', sensor: 'humidity', operator: '<', value: 40 }] }` evaluates correctly
- Nested composite triggers work up to depth 5, then return false with a warning
- Existing sensor-only triggers still work
</acceptance_criteria>

> **v1 Scope Limitation:** Composite triggers are limited to same-type sub-triggers in v1.
> - **Sensor composites** work: all sub-triggers evaluated in the same `tick()` call
> - **Event composites** work: all sub-triggers evaluated in the same `handleEvent()` call
> - **Cross-type composites** (sensor + event) do NOT work in v1 because `tick()` and `handleEvent()` are separate code paths that never run simultaneously. A sensor sub-trigger can't "remember" that an event fired earlier.
>
> Cross-type composites require a stateful evaluation layer (e.g., event flags that persist across ticks) — deferred to Phase 8+. Document this limitation clearly in types.ts.

---

### Task 3: Enforce modeFilter gate (G3)

<read_first>
- `harness/src/engine/SkillExecutor.ts` (lines 383-385 — `matchesSpace`)
- `harness/src/shared/types.ts` (CoreSkill.modeFilter field)
</read_first>

<action>
Update `matchesSpace()` to enforce `modeFilter`:

```typescript
private matchesSpace(skill: CoreSkill): boolean {
  const spaceMatch = skill.spaceId === '*' || skill.spaceId === this.opts.spaceId;
  const modeMatch = !skill.modeFilter || skill.modeFilter === this.activeMode;
  return spaceMatch && modeMatch;
}
```

This is a 3-line change. Skills without `modeFilter` (undefined) match all modes. Skills with `modeFilter: 'student'` only fire when `activeMode === 'student'`.
</action>

<acceptance_criteria>
- A skill with `modeFilter: 'student'` does NOT fire when `activeMode === 'family'`
- A skill with `modeFilter: 'student'` DOES fire when `activeMode === 'student'`
- A skill without `modeFilter` (undefined) fires in all modes
</acceptance_criteria>

---

### Task 4: Remove `_idle-sleep` builtin (G4)

<read_first>
- `harness/src/engine/builtins.ts`
- `harness/src/shared/contracts.ts` (BUILTIN_SKILL_IDS)
</read_first>

<action>
1. Remove `IDLE_SLEEP` export and its definition from `builtins.ts`.
2. Remove `'_idle-sleep'` from `BUILTIN_SKILL_IDS` array in `contracts.ts`.
3. Remove `IDLE_SLEEP` from `ALL_BUILTINS` array.
4. Verify `ModeManager` already has idle timer logic that handles listen→sleep after 60s — no changes needed there.
</action>

<acceptance_criteria>
- `BUILTIN_SKILL_IDS` no longer contains `'_idle-sleep'`
- `ALL_BUILTINS` has 3 entries: `_pir-wake`, `_sensor-telemetry`, `_determine-skill`
- ModeManager still transitions listen→sleep on its idle timer
- No import errors or references to `IDLE_SLEEP`
</acceptance_criteria>

---

### Task 5: Implement DataCollector auto-collect + auto-reset (G5)

<read_first>
- `harness/src/engine/SkillExecutor.ts` (lines 214-251 — `fireSkill`, lines 280-284 — `increment_counter` action)
- `harness/src/shared/types.ts` (DataCollector interface)
</read_first>

<action>
1. Add `counterResetTimers: Map<string, NodeJS.Timeout>` to `SkillExecutor` class.

2. In `fireSkill()`, after incrementing `fireCount` and before executing L1 actions, auto-collect DataCollectors:

```typescript
private fireSkill(skill: CoreSkill, triggerData: Record<string, unknown>): void {
  const now = Date.now();
  if (skill.cooldownMs && skill.lastFiredAt && (now - skill.lastFiredAt < skill.cooldownMs)) {
    logger.debug({ skillId: skill.id }, 'Skill skipped (cooldown)');
    return;
  }

  skill.lastFiredAt = now;
  skill.fireCount++;

  // Auto-collect DataCollectors
  if (skill.collect) {
    for (const dc of skill.collect) {
      if (dc.type === 'counter') {
        const cur = this.counters.get(dc.name) ?? 0;
        this.counters.set(dc.name, cur + 1);

        // Auto-reset after resetAfterMs
        if (dc.resetAfterMs) {
          const timerKey = `${skill.id}:${dc.name}`;
          const existing = this.counterResetTimers.get(timerKey);
          if (existing) clearTimeout(existing);
          const handle = setTimeout(() => {
            this.counters.set(dc.name, 0);
            this.counterResetTimers.delete(timerKey);
            logger.debug({ counterName: dc.name }, 'Counter auto-reset');
          }, dc.resetAfterMs);
          this.counterResetTimers.set(timerKey, handle);
        }
      }
    }
  }

  const actionsExecuted = this.executeL1Actions(skill, triggerData);
  // ... rest of fireSkill unchanged
}
```

3. In `removeSkill()`, clean up any reset timers associated with the removed skill's collectors:

```typescript
removeSkill(id: string): boolean {
  if ((BUILTIN_SKILL_IDS as readonly string[]).includes(id)) {
    logger.warn({ id }, 'Cannot remove builtin skill');
    return false;
  }
  const skill = this.skills.get(id);
  if (skill?.collect) {
    for (const dc of skill.collect) {
      const timerKey = `${id}:${dc.name}`;
      const handle = this.counterResetTimers.get(timerKey);
      if (handle) { clearTimeout(handle); this.counterResetTimers.delete(timerKey); }
    }
  }
  this.teardownSkillSchedule(id);
  return this.skills.delete(id);
}
```

4. In `stop()`, clear all reset timers:

```typescript
stop(): void {
  // ... existing cleanup ...
  for (const [, handle] of this.counterResetTimers) clearTimeout(handle);
  this.counterResetTimers.clear();
}
```
</action>

<acceptance_criteria>
- A skill with `collect: [{ type: 'counter', name: 'motionCount', resetAfterMs: 30000 }]` auto-increments `motionCount` on each fire
- After `resetAfterMs`, the counter auto-resets to 0
- If the same skill fires again before reset, the reset timer restarts (debounced)
- Removing a skill clears its counter reset timers
- `SkillExecutor.stop()` clears all timers
</acceptance_criteria>

---

## Verification

```bash
cd harness && npx tsc --noEmit
cd harness && npx vitest run
```

Both must exit 0.

<must_haves>
- Mode trigger `{ type: 'mode', from, to }` fires on SpaceMode transitions
- Composite trigger `{ type: 'composite', all: [...] }` evaluates all sub-triggers with AND logic
- `modeFilter` on CoreSkill prevents firing in non-matching behavioral modes
- `_idle-sleep` removed from builtins and BUILTIN_SKILL_IDS
- DataCollector auto-collects counters on fire and auto-resets after `resetAfterMs`
- All existing tests pass
</must_haves>
