daviddatuX25/Xentient/.planning/phases/07-skill-engine-hardening/07-02-PLAN.md

---
wave: 1
depends_on: none
files_modified:
  - harness/src/comms/EventBridge.ts
  - harness/src/core.ts
  - harness/src/engine/SpaceManager.ts
autonomous: true
requirements: [PT-03, PT-04]
---

# Plan 07-02: Generic MQTT Event Bridge

## Goal
Replace hardcoded MQTT event routing in `core.ts` with a configurable event bridge. Any MQTT topic can be mapped to a named event that skills can trigger on, eliminating the need to modify `core.ts` for new sensor types or event sources.

---

## Tasks

### Task 1: Create EventBridge module

<read_first>
- `harness/src/core.ts` (lines 138-164 — hardcoded event routing)
- `harness/src/comms/MqttClient.ts` (MQTT subscription API)
- `harness/src/engine/SpaceManager.ts` (handleEvent method)
</read_first>

<action>
Create `harness/src/comms/EventBridge.ts`:

```typescript
import { EventEmitter } from 'events';
import pino from 'pino';
import { MqttClient } from './MqttClient';
import { SpaceManager } from '../engine/SpaceManager';
import { ModeManager } from '../engine/ModeManager';
import { PERIPHERAL_IDS } from '../shared/contracts';

const logger = pino({ name: 'event-bridge' }, process.stderr);

export interface EventMapping {
  /** Event source — uses MqttClient event names, NOT raw MQTT topics.
   *  MqttClient already multiplexes MQTT topics into named events
   *  ('sensor', 'triggerPipeline', 'modeCommand'). The EventBridge
   *  subscribes to these MqttClient events, not to raw MQTT topics.
   *  This avoids the topic-stripping problem: MqttClient.handleMessage()
   *  maps MQTT topics to named events but discards the topic name
   *  before emitting. Filtering by peripheralType/source+stage works
   *  because those fields are preserved in the parsed data. */
  source: 'mqtt:sensor' | 'mqtt:triggerPipeline' | 'mode' | 'custom';
  /** Filter function. Return false to skip this event.
   *  For mqtt:sensor source, filter by peripheralType.
   *  For mqtt:triggerPipeline source, filter by source+stage. */
  filter?: (data: unknown) => boolean;
  /** Named event name forwarded to SpaceManager.handleEvent() */
  eventName: string;
  /** Transform raw data into triggerData for the skill system */
  transform?: (data: unknown) => Record<string, unknown>;
}

export const DEFAULT_EVENT_MAPPINGS: EventMapping[] = [
  // PIR motion → motion_detected
  {
    source: 'mqtt:sensor',
    filter: (data: unknown) => {
      const d = data as { peripheralType?: number; payload?: { motion?: boolean } };
      return d.peripheralType === PERIPHERAL_IDS.PIR && d.payload?.motion === true;
    },
    eventName: 'motion_detected',
    transform: (data: unknown) => {
      const d = data as { payload?: { motion?: boolean } };
      return { motion: true, timestamp: Date.now() };
    },
  },
  // BME280 sensor update → sensor_update
  {
    source: 'mqtt:sensor',
    filter: (data: unknown) => {
      const d = data as { peripheralType?: number };
      return d.peripheralType === PERIPHERAL_IDS.BME280;
    },
    eventName: 'sensor_update',
    transform: (data: unknown) => {
      const d = data as { payload?: Record<string, unknown> };
      return { ...d.payload, timestamp: Date.now() };
    },
  },
  // Voice start → voice_start
  {
    source: 'mqtt:triggerPipeline',
    filter: (data: unknown) => {
      const d = data as { source?: string; stage?: string };
      return d.source === 'voice' && d.stage === 'start';
    },
    eventName: 'voice_start',
    transform: () => ({ timestamp: Date.now() }),
  },
  // Voice end → voice_end
  {
    source: 'mqtt:triggerPipeline',
    filter: (data: unknown) => {
      const d = data as { source?: string; stage?: string };
      return d.source === 'voice' && d.stage === 'end';
    },
    eventName: 'voice_end',
    transform: () => ({ timestamp: Date.now() }),
  },
  // ModeManager transitions → mode_transition
  {
    source: 'mode',
    eventName: 'mode_transition',
    transform: (data: unknown) => {
      const { from, to } = data as { from: string; to: string };
      return { from, to, timestamp: Date.now() };
    },
  },
];

export class EventBridge extends EventEmitter {
  private mappings: Map<string, EventMapping> = new Map();

  constructor(
    private mqtt: MqttClient,
    private spaceManager: SpaceManager,
    private modeManager: ModeManager,
  ) {
    super();
  }

  start(mappings: EventMapping[] = DEFAULT_EVENT_MAPPINGS): void {
    for (const mapping of mappings) {
      this.register(mapping);
    }

    // Wire MqttClient events — subscribe to named events, NOT raw MQTT topics
    this.mqtt.on('sensor', (data: unknown) => {
      this.handleMqttEvent('mqtt:sensor', data);
    });
    this.mqtt.on('triggerPipeline', (data: unknown) => {
      this.handleMqttEvent('mqtt:triggerPipeline', data);
    });

    // Wire ModeManager transitions
    this.modeManager.on('modeChange', ({ from, to }: { from: string; to: string }) => {
      this.forwardModeEvent(from, to);
    });

    logger.info({ count: this.mappings.size }, 'EventBridge started');
  }

  register(mapping: EventMapping): string {
    const id = `${mapping.source}:${mapping.eventName}`;
    this.mappings.set(id, mapping);
    return id;
  }

  /** Route a MqttClient named event to matching EventMappings */
  handleMqttEvent(mqttEventName: 'mqtt:sensor' | 'mqtt:triggerPipeline', data: unknown): void {
    for (const [id, mapping] of this.mappings) {
      if (mapping.source !== mqttEventName) continue;
      if (mapping.filter && !mapping.filter(data)) continue;
      const triggerData = mapping.transform ? mapping.transform(data) : {};
      this.spaceManager.handleEvent(mapping.eventName, triggerData);
      this.emit('event_forwarded', { mappingId: id, eventName: mapping.eventName });
    }
  }

  /** Called by ModeManager when hardware mode transitions */
  private forwardModeEvent(from: string, to: string): void {
    for (const [, mapping] of this.mappings) {
      if (mapping.source !== 'mode') continue;
      const triggerData = mapping.transform ? mapping.transform({ from, to }) : { from, to };
      this.spaceManager.handleEvent(mapping.eventName, triggerData);
      this.emit('event_forwarded', { mappingId: `mode:${mapping.eventName}`, eventName: mapping.eventName });
    }
  }

  /** Add a custom event mapping at runtime (via MCP tool) */
  addCustomMapping(source: EventMapping['source'], eventName: string, filter?: (data: unknown) => boolean, transform?: (data: unknown) => Record<string, unknown>): string {
    const mapping: EventMapping = {
      source,
      eventName,
      filter,
      transform,
    };
    return this.register(mapping);
  }

  removeMapping(id: string): boolean {
    return this.mappings.delete(id);
  }

  listMappings(): EventMapping[] {
    return Array.from(this.mappings.values());
  }

  stop(): void {
    this.mappings.clear();
    logger.info('EventBridge stopped');
  }
}
```
</action>

<acceptance_criteria>
- `EventBridge` class exists in `harness/src/comms/EventBridge.ts`
- Default mappings preserve existing behavior (PIR, BME280, voice, mode transitions)
- Custom mappings can be added/removed at runtime
- ModeManager transitions are forwarded as `mode_transition` events
- No hardcoded MQTT event routing remains in `core.ts`
</acceptance_criteria>

---

### Task 2: Refactor core.ts to use EventBridge

<read_first>
- `harness/src/core.ts` (lines 138-164 — current hardcoded wiring)
</read_first>

<action>
Replace the hardcoded event routing in `core.ts` (lines 138-164) with EventBridge:

```typescript
// REMOVE these blocks:
// - mqtt.on("sensor", ...) handler (lines 140-149) — replaced by EventBridge
// - mqtt.on("triggerPipeline", ...) handler for voice events (lines 152-158) — replaced by EventBridge
// - modeManager.on("modeChange", ...) handler that calls spaceManager.switchMode (lines 161-164) — replaced by EventBridge

// ADD:
import { EventBridge, DEFAULT_EVENT_MAPPINGS } from './comms/EventBridge';

// After spaceManager creation:
const eventBridge = new EventBridge(mqtt, spaceManager, modeManager);
// EventBridge.start() internally subscribes to mqtt 'sensor' and 'triggerPipeline' events
eventBridge.start(DEFAULT_EVENT_MAPPINGS);

// Sensor cache updates stay in core.ts — they're data collection, not event routing
mqtt.on("sensor", (data: unknown) => {
  const d = data as { peripheralType?: number; payload?: Record<string, unknown> };
  if (d.peripheralType === PERIPHERAL_IDS.BME280 && d.payload) {
    if (d.payload.temperature !== undefined) sensorCache.temperature = d.payload.temperature as number;
    if (d.payload.humidity !== undefined) sensorCache.humidity = d.payload.humidity as number;
    if (d.payload.pressure !== undefined) sensorCache.pressure = d.payload.pressure as number;
  }
  if (d.peripheralType === PERIPHERAL_IDS.PIR && d.payload?.motion) {
    sensorCache.lastMotionAt = Date.now();
    sensorCache.motion = 1;
  }
});

// Mode change still syncs SpaceMode on the Space object
modeManager.on("modeChange", ({ to }) => {
  spaceManager.updateSpaceMode('default', to);
  logger.info({ mode: to }, 'SpaceMode synced with ModeManager');
});

// Voice-end audio flush logic stays in core.ts (not skill-system concern)
mqtt.on("triggerPipeline", (data: unknown) => {
  const d = data as { source?: string; stage?: string };
  if (d.source === "voice" && d.stage === "end" && isAccumulating) {
    // ... existing audio flush logic stays here ...
  }
});
```

> **Note: Dual MQTT event path with `mcp/events.ts`**
>
> After this change, both `mcp/events.ts` and `EventBridge` handle the same MQTT events:
> 1. **`mcp/events.ts`** → sensor cache updates + MCP notifications to Brain (via `server.notification()`)
> 2. **`EventBridge** → skill event dispatch (via `spaceManager.handleEvent()`)
>
> Both are explicitly called from `core.ts`. This is intentional — they serve different purposes:
> - `mcp/events.ts` is the **Brain notification layer** (pushes events to the connected AI)
> - `EventBridge` is the **skill trigger layer** (activates skills based on events)
>
> Do NOT merge these two systems. They have different lifecycles, different subscribers, and different failure modes.
</action>

<acceptance_criteria>
- `core.ts` no longer has hardcoded `if (d.peripheralType === PERIPHERAL_IDS.PIR)` event routing
- Event routing is handled entirely by `EventBridge`
- Sensor cache updates still happen (for MCP tool reads)
- Audio flush logic still works (voice_end handling)
- All existing behavior preserved
</acceptance_criteria>

---

### Task 3: Add MCP tool for custom event mapping

<read_first>
- `harness/src/mcp/tools.ts` (existing tool registration pattern)
</read_first>

<action>
Add `xentient_register_event_mapping` and `xentient_remove_event_mapping` MCP tools to allow the Brain to register custom event mappings at runtime.

This is a v1 tool — the Brain can:
- Register a new event mapping (source + eventName, with optional filter/transform)
- Remove a mapping
- List current mappings

The MCP tool handler gets a reference to the `EventBridge` instance (passed via deps).

Add to `contracts.ts`:
```typescript
export const EVENT_BRIDGE_TOOLS = {
  REGISTER_MAPPING: 'xentient_register_event_mapping',
  REMOVE_MAPPING: 'xentient_remove_event_mapping',
  LIST_MAPPINGS: 'xentient_list_event_mappings',
} as const;
```

Add to `tools.ts` following the existing pattern. Schema:
- `xentient_register_event_mapping`: `{ source: 'mqtt:sensor' | 'mqtt:triggerPipeline' | 'custom', eventName: string }`
- `xentient_remove_event_mapping`: `{ mappingId: string }`
- `xentient_list_event_mappings`: `{}` (no params)
</action>

<acceptance_criteria>
- Brain can call `xentient_register_event_mapping` with `{ source: "mqtt:sensor", eventName: "button_pressed" }` (filter function provided at registration)
- A skill with `trigger: { type: 'event', event: 'button_pressed' }` fires when a matching MqttClient sensor event arrives
- Brain can list and remove custom mappings
- Default mappings cannot be removed via MCP (they're protected)
</acceptance_criteria>

---

## Verification

```bash
cd harness && npx tsc --noEmit
cd harness && npx vitest run
```

Both must exit 0. Integration test: register a custom event mapping, send a matching MQTT message, verify the skill fires.

<must_haves>
- EventBridge replaces all hardcoded MQTT event routing in core.ts
- Default mappings preserve PIR, BME280, voice, and mode_transition events
- Custom MQTT topic → event mappings registerable via MCP tool
- Mode transitions forwarded as `mode_transition` events (G1 partial — full wiring in 07-01)
- No behavior change for existing functionality
</must_haves>
