daviddatuX25/Xentient/.planning/phases/07-skill-engine-hardening/07-05-PLAN.md

---
wave: 3
depends_on: [07-01, 07-02, 07-03, 07-04]
files_modified:
  - harness/tests/SkillExecutor.gaps.test.ts
  - harness/tests/EventBridge.test.ts
  - harness/tests/PackLoader.test.ts
  - harness/tests/SkillPersistence.test.ts
autonomous: true
requirements: [PT-03, PT-04]
---

# Plan 07-05: Tests for Phase 7 Gap Fixes

## Goal
Comprehensive Vitest tests for all Phase 7 gap fixes: mode triggers, composite evaluation, modeFilter, _idle-sleep removal, DataCollector auto-collect/reset, EventBridge, PackLoader, and SkillPersistence.

---

## Tasks

### Task 1: SkillExecutor gap fix tests

<read_first>
- `harness/tests/SkillExecutor.test.ts` (existing test patterns)
- `harness/src/engine/SkillExecutor.ts` (updated with G1-G5 fixes)
- `harness/src/shared/types.ts` (CoreSkill, SkillTrigger)
</read_first>

<action>
Create `harness/tests/SkillExecutor.gaps.test.ts` covering:

**G1 — Mode trigger evaluation:**
- Skill with `{ type: 'mode', from: 'sleep', to: 'listen' }` fires on `handleEvent('mode_transition', { from: 'sleep', to: 'listen' })`
- Wildcard mode trigger `{ type: 'mode', from: '*', to: 'listen' }` matches any → listen transition
- Wildcard mode trigger `{ type: 'mode', from: 'sleep', to: '*' }` matches any sleep→* transition
- Mode trigger does NOT fire for non-matching transitions (e.g., from: 'sleep', to: 'listen' doesn't match from: 'listen', to: 'active')

**G2 — Composite trigger evaluation:**
- Composite trigger with single sensor sub-trigger evaluates correctly
- Composite trigger with multiple sensor sub-triggers evaluates with AND logic
- Nested composite trigger works (depth 2)
- Composite trigger depth limit (depth > 5 returns false)
- **v1 limitation verified:** Composite with mixed sensor+event sub-triggers does NOT fire (documented, not a bug)

**G3 — modeFilter enforcement:**
- Skill with `modeFilter: 'student'` fires when `activeMode === 'student'`
- Skill with `modeFilter: 'student'` does NOT fire when `activeMode === 'family'`
- Skill without `modeFilter` (undefined) fires in all modes

**G4 — _idle-sleep removed:**
- `BUILTIN_SKILL_IDS` does not contain `'_idle-sleep'`
- `ALL_BUILTINS` has 3 entries (pir-wake, sensor-telemetry, determine-skill)
- ModeManager's idle timer still transitions listen→sleep after 60s

**G5 — DataCollector auto-collect + reset:**
- Skill with `collect: [{ type: 'counter', name: 'motionCount' }]` auto-increments counter on fire
- Skill with `collect: [{ type: 'counter', name: 'motionCount', resetAfterMs: 30000 }]` resets counter after 30s
- Counter reset timer restarts if skill fires again before reset
- Removing a skill clears its counter reset timers
- `SkillExecutor.stop()` clears all timers
</action>

<acceptance_criteria>
- All G1-G5 test cases pass
- Test coverage for `evaluateTrigger`, `matchesSpace`, `handleEvent` mode branch
- Counter reset timer tests use `vi.useFakeTimers()` for deterministic timing
</acceptance_criteria>

---

### Task 2: EventBridge tests

<read_first>
- `harness/src/comms/EventBridge.ts`
</read_first>

<action>
Create `harness/tests/EventBridge.test.ts` covering:

- Default mappings load on `start()`
- `handleMqttEvent('mqtt:sensor', data)` with PIR data forwards as `motion_detected`
- `handleMqttEvent('mqtt:sensor', data)` with BME280 data forwards as `sensor_update`
- `handleMqttEvent('mqtt:triggerPipeline', data)` with voice start forwards as `voice_start`
- Mode transition forwards as `mode_transition`
- `addCustomMapping()` registers a new event mapping (source + eventName)
- `removeMapping()` removes a mapping
- `listMappings()` returns all current mappings
- Custom mapping with filter function only forwards matching messages
- Custom mapping with transform function transforms data before forwarding
- `stop()` clears all mappings
</action>

<acceptance_criteria>
- All EventBridge tests pass
- Default mappings cover PIR, BME280, voice, mode transitions
- Custom mappings work at runtime
</acceptance_criteria>

---

### Task 3: PackLoader tests

<read_first>
- `harness/src/engine/PackLoader.ts`
</read_first>

<action>
Create `harness/tests/PackLoader.test.ts` covering:

- `loadPack('default')` loads skills from `packs/default/skills.json`
- Loaded skills have `source: 'pack'`
- Loaded skills have `spaceId: '*'` (global) and `priority: 50` default
- Zod validation rejects malformed manifest (missing fields, wrong types)
- `loadPack()` throws if a pack skill ID starts with `_` (builtin namespace collision)
- `loadPack()` unloads previous pack before loading new one
- `unloadCurrentPack()` only removes pack skills, preserves brain/builtin skills
- `listAvailablePacks()` returns pack names with valid `skills.json`
- `reload()` re-reads manifest and re-registers skills
- Loading non-existent pack throws error
</action>

<acceptance_criteria>
- All PackLoader tests pass
- Default pack loads correctly
- Pack switch preserves brain/builtin skills
- Zod validation catches malformed manifests
</acceptance_criteria>

---

### Task 4: SkillPersistence tests

<read_first>
- `harness/src/engine/SkillPersistence.ts`
</read_first>

<action>
Create `harness/tests/SkillPersistence.test.ts` covering:

- `load()` returns empty array when file doesn't exist
- `load()` returns brain-registered skills from valid file
- `load()` ignores non-brain skills (source: 'builtin', 'pack') in the file
- `load()` returns empty array on malformed JSON (no crash)
- `save()` writes only `source: 'brain'` skills to file
- `save()` creates data directory if it doesn't exist
- Round-trip: save skills, load them back, all brain skills present
- `save()` filters out builtin and pack skills (they're loaded from other sources)
</action>

<acceptance_criteria>
- All SkillPersistence tests pass
- Round-trip save/load works for brain skills
- Malformed file doesn't crash
- Only brain skills are persisted
</acceptance_criteria>

---

## Verification

```bash
cd harness && npx vitest run
```

All tests must pass. Total test count should increase by ~30-40 tests across 4 new test files.

<must_haves>
- SkillExecutor gap tests (G1-G5) all pass
- EventBridge tests pass
- PackLoader tests pass
- SkillPersistence tests pass
- Full test suite exits 0
</must_haves>
