daviddatuX25/Xentient/.planning/phases/08-web-console-dashboard/08-05-SUMMARY.md

---
phase: 8
plan: 08-05
subsystem: frontend+backend
tags: [telemetry, sparklines, canvas, retina-dpi, ring-buffer, motion-timeline, mode-timeline, skill-log, escalation-feed, conflict-log, batched-dom-updates, sse-realtime]

# Dependency graph
requires:
  - phase: 08-01
    provides: [/api/sensors/history endpoint, /api/skill-log endpoint]
  - phase: 08-02
    provides: [sensor_update, mode_change, skill_fired, skill_escalated, skill_conflict SSE events]
  - phase: 08-03
    provides: [SPA shell, CSS design system, api.js REST client, sse.js client, main.js routing]
provides:
  - ModeHistory ring buffer class (100 intervals, open-ended current mode)
  - SensorHistory enhanced with 1s throttle and clear() method
  - MotionHistory already existed from prior work
  - GET /api/sensors/motion-history?minutes=30 endpoint
  - GET /api/mode/history?minutes=30 endpoint
  - ControlServerDeps: motionHistory and modeHistory interfaces
  - TelemetryPanel with Sparkline class (canvas, retina DPI, flat-line centering)
  - Motion timeline (30min window, dot rendering for PIR events)
  - Mode timeline (30min window, color-coded blocks per interval, legend)
  - Skill fire log (reverse-chronological, batched DOM updates via rAF)
  - Escalation feed (color-coded cards, collapsible context JSON)
  - Conflict log (skills vs winner display)
  - SSE-driven live updates for all telemetry components
  - Data seeding on first load and SSE reconnect
affects: [08-06, 08-08]

# Tech tracking
tech-stack:
  added: [canvas-sparkline, ring-buffer-pattern, batched-dom-updates]
  patterns: [retina-dpi-canvas-setup, flat-line-centering-when-range-zero, sse-reconnect-data-reseeding, requestAnimationFrame-batched-updates, css-custom-property-for-sparkline-color]

key-files:
  created:
    - harness/src/engine/ModeHistory.ts (new ring buffer for mode transition intervals)
  modified:
    - harness/src/engine/SensorHistory.ts (+throttle, +clear method)
    - harness/src/comms/ControlServer.ts (+MotionHistoryLike, +ModeHistoryLike deps, +2 endpoints)
    - harness/src/core.ts (+MotionHistory/ModeHistory imports, instantiation, wiring)
    - harness/src/index.ts (+stub motionHistory/modeHistory deps)
    - harness/public/js/telemetry.js (full TelemetryPanel replacing placeholder)
    - harness/public/js/api.js (+getMotionHistory, +getModeHistory)
    - harness/public/js/main.js (+telemetry SSE dispatch, +reseed on reconnect)
    - harness/public/dashboard.css (+250 lines telemetry CSS)

key-decisions:
  - "SensorHistory throttle set to 1 entry/second to prevent ring buffer overflow from high-frequency sensor bursts"
  - "ModeHistory seeded with current mode on startup via recordTransition(modeManager.getMode()) so mode timeline is never empty"
  - "Sparkline color read from CSS --sparkline-color custom property on canvas element rather than hardcoded -- allows theme consistency"
  - "Escalation context skips camera frame (no base64 JPEG in dashboard for v1) per plan spec"
  - "SSE dispatch for telemetry events stays in main.js (same pattern as skills.js) — telemetry.js exports handler functions"

patterns-established:
  - "Canvas retina DPI: read devicePixelRatio, scale context, set style dimensions separately from canvas dimensions"
  - "Flat-line centering: when all values are identical (range=0), draw line at h/2 instead of top/bottom edge"
  - "Batched DOM updates: pendingUpdates array + requestAnimationFrame for high-frequency skill fires"
  - "Ring buffer query pattern: query(sinceMs?) with Date.now()-sinceMs cutoff filter"

requirements-completed: []

# Metrics
duration: 15min
completed: 2026-04-28
---

# Phase 8 Plan 05: Live Telemetry & Event Feed Summary

**Canvas sparklines with retina DPI, motion/mode timelines, skill fire log with batched DOM updates, escalation/conflict feeds, and three ring buffer classes for server-side history**

## Performance

- **Duration:** 15 min
- **Started:** 2026-04-28T22:09:04Z
- **Completed:** 2026-04-28T22:24:06Z
- **Tasks:** 3 (ring buffers + server wiring + frontend panel)
- **Files modified:** 9 (1 new, 8 modified)

## Accomplishments
- ModeHistory ring buffer records mode transitions as time intervals with open-ended current mode
- SensorHistory enhanced with 1 entry/second throttle (prevents overflow) and clear() method
- MotionHistory already existed (from prior phase 7 post-implementation)
- Two new REST endpoints: GET /api/sensors/motion-history?minutes=30 and GET /api/mode/history?minutes=30
- ControlServerDeps interface expanded with MotionHistoryLike and ModeHistoryLike structural types
- core.ts: MotionHistory and ModeHistory instantiated, wired to PIR sensor handler and mode_change event, seeded current mode on startup
- TelemetryPanel with 6 components: temperature/humidity/pressure sparklines, motion timeline, mode timeline, skill fire log, escalation feed, conflict log
- Sparkline class renders on Canvas with retina DPI handling, flat-line centering when range=0, resize debouncing at 200ms
- Motion timeline renders PIR events as amber dots in 30min window
- Mode timeline renders color-coded blocks per mode interval with legend (sleep/listen/active/record HSL colors)
- Skill fire log uses batched DOM updates via requestAnimationFrame for high-frequency events
- Escalation feed shows color-coded cards (critical=red, high=amber, normal=emerald) with collapsible context JSON
- Conflict feed shows conflicting skills with winner resolution
- All colors use xai-DESIGN.md tokens (CSS custom properties, HSL mode colors)
- Data seeded on first load from REST endpoints; re-seeded on SSE reconnect

## Task Commits

Each task was committed atomically:

1. **ModeHistory ring buffer + SensorHistory throttling** - `00bbfe5` (feat)
2. **Wire MotionHistory/ModeHistory into core.ts, add REST endpoints** - `f1ed942` (feat)
3. **Telemetry panel implementation (sparklines, timelines, event feeds, CSS)** - `a8fd5e5` (feat)

## Files Created/Modified
- `harness/src/engine/ModeHistory.ts` - Ring buffer for mode transition intervals (100 max), recordTransition/query
- `harness/src/engine/SensorHistory.ts` - Added 1s throttle (intervalMs=1000), clear() method, push uses push-time timestamp
- `harness/src/comms/ControlServer.ts` - Added MotionHistoryLike/ModeHistoryLike interfaces, motion-history and mode-history endpoints, updated deps
- `harness/src/core.ts` - Imported/instantiated MotionHistory+ModeHistory, wired PIR sensor to motionHistory.push(), wired mode_change to modeHistory.recordTransition(), seeded current mode, passed to ControlServerDeps
- `harness/src/index.ts` - Added stub motionHistory/modeHistory deps for basic mode entry point
- `harness/public/js/telemetry.js` - Full TelemetryPanel: Sparkline class (retina DPI, flat-line centering), motion/mode timelines, skill fire log, escalation feed, conflict feed, batched DOM updates, data seeding
- `harness/public/js/api.js` - Added getMotionHistory(minutes) and getModeHistory(minutes) methods
- `harness/public/js/main.js` - Wired telemetry SSE handlers (sensor_update, skill_fired, skill_escalated, skill_conflict, mode_change), re-seed on reconnect
- `harness/public/dashboard.css` - +250 lines: sparkline rows/canvas, motion timeline (dot + bar), mode timeline (blocks + legend), skill log entries, escalation cards (header + context), conflict cards, responsive breakpoints

## Decisions Made
- SensorHistory throttle set to 1 entry/second to prevent ring buffer overflow from high-frequency sensor bursts. Without throttling, 300-capacity buffer at 10Hz sensor rate would only hold 30 seconds of data.
- ModeHistory seeded with current mode on startup via `modeHistory.recordTransition(modeManager.getMode())` so the mode timeline is never empty even if no mode transitions occur during the session.
- Sparkline color read from CSS `--sparkline-color` custom property on the canvas element rather than hardcoded. Each canvas sets its own `--sparkline-color` inline style, keeping theme consistency.
- Escalation context skips camera frame (no base64 JPEG in dashboard for v1) per plan spec. The context JSON is shown in a collapsible `<details>` element.
- SSE dispatch for telemetry events stays in main.js (same pattern as skills.js) -- telemetry.js exports handler functions that main.js calls in the event switch.

## Deviations from Plan

None - plan executed exactly as written.

## Issues Encountered

None -- plan executed cleanly with no blockers.

## Known Stubs

| File | Stub | Reason | Resolution |
|---|---|---|---|
| `harness/src/index.ts` | motionHistory/modeHistory are empty stubs (`{ query: () => [] }`) | Basic mode entry point doesn't run skill engine or history tracking | Full wiring only in core.ts; basic mode is legacy entry point |

## Threat Flags

No new threat surface. The motion-history and mode-history endpoints are read-only GET routes that return in-memory ring buffer data. No authentication (v1 single-user). The 64KB body size limit from 08-07 applies to POST endpoints only. Ring buffers have bounded capacity (MotionHistory 180, ModeHistory 100, SensorHistory 300) preventing memory exhaustion.

## Self-Check: PASSED

- All 9 created/modified files verified on disk
- Commit `00bbfe5` verified in git log (feat: ModeHistory + SensorHistory throttling)
- Commit `f1ed942` verified in git log (feat: wire MotionHistory/ModeHistory into core.ts)
- Commit `a8fd5e5` verified in git log (feat: telemetry panel implementation)
- TypeScript compiles with 0 errors
- No accidental file deletions in any commit
- No untracked generated files

## Next Phase Readiness
- 08-06 (Mode & Space Controls) can proceed: api.js has mode/space endpoints, sse.js handles mode_change, mode.js placeholder exists
- 08-08 (Integration Testing) can proceed: all telemetry endpoints and frontend components are testable
- All CSS design tokens and component patterns (card, toast, gauge, badge, drawer) are reusable by downstream panels

---
*Phase: 08-web-console-dashboard*
*Completed: 2026-04-28*
