daviddatuX25/Xentient/.planning/phases/08-web-console-dashboard/08-02-PLAN.md

---
plan: 08-02
title: SSE Event Expansion
phase: 8
wave: 1 (backend)
depends_on: [08-07]
hard_points: [H5]
estimated_files: 5
estimated_loc: 300
---

# 08-02: SSE Event Expansion

## Goal

Expand the SSE endpoint (`/api/events`) to push all events the dashboard needs for real-time updates. Add lifecycle events for skills, packs, and event mappings. Add throttled sensor updates and counter updates.

## Prerequisites

- **08-07 complete** — ControlServer must accept SpaceManager, EventBridge, PackLoader, SkillLog as deps

## Resolved Prerequisites (from Phase 7 post-implementation)

- **`broadcastSSE` visibility (Expansion 2.1):** `broadcastSSE` is `private`, but `broadcastSkillEvent()` is already `public` (line 253) and just calls `broadcastSSE()`. **Decision:** Rename `broadcastSkillEvent` → `broadcastSSE` and make it `public`. The current `broadcastSkillEvent` name is misleading since it broadcasts any SSE event, not just skill events. The old `private broadcastSSE` becomes the internal implementation detail.
- **EventBridge events (Expansion 2.3):** **CONFIRMED** — `mappingAdded` at line 217 and `mappingRemoved` at line 230 both exist with correct payloads. No additional work needed.

## New SSE Event Types

| Event Type | Trigger | Payload |
|---|---|---|
| `skill_registered` | `SpaceManager.registerSkill()` | `{ skillId, source, triggerType }` |
| `skill_removed` | `SpaceManager.removeSkill()` | `{ skillId }` |
| `skill_updated` | `SpaceManager.updateSkill()` / `disableSkill()` | `{ skillId, patch }` |
| `pack_loaded` | `PackLoader.loadPack()` | `{ packName, skillCount }` |
| `pack_unloaded` | `PackLoader.unloadCurrentPack()` | `{ packName }` |
| `event_mapping_added` | `EventBridge.addCustomMapping()` | `{ mappingId, source, eventName }` |
| `event_mapping_removed` | `EventBridge.removeMapping()` | `{ mappingId }` |
| `sensor_update` | sensorCache change | `{ temperature, humidity, pressure }` (throttled 1/s) |
| `counter_update` | SkillExecutor counter change | `{ counters: Record<string, number> }` (throttled 1/s) |
| `mode_change` | ModeManager transition | `{ from, to, timestamp }` (for mode history — Expansion 5.5) |

### Already-Existing Events (unchanged)

| Event Type | Trigger |
|---|---|
| `connected` | SSE connection init |
| `mode_status` | MQTT modeStatus |
| `pipeline_state` | MQTT pipelineState |
| `session_complete` | MQTT sessionComplete |
| `session_error` | MQTT sessionError |
| `transcript` | POST /api/text |
| `skill_fired` | SpaceManager observability |
| `skill_escalated` | SpaceManager observability |
| `skill_conflict` | SpaceManager observability |

### SSE Event Schema Documentation (Expansion 2.4)

Every SSE event type must have a documented TypeScript type definition so the frontend can type-check. Add a type definition block:

```typescript
// In harness/src/comms/sse-types.ts (NEW) or inline in ControlServer.ts

export interface SSEEventMap {
  connected: { type: 'connected' };
  mode_status: { type: 'mode_status'; mode: string };
  mode_change: { type: 'mode_change'; from: string; to: string; timestamp: number };
  pipeline_state: { type: 'pipeline_state'; state: string };
  session_complete: { type: 'session_complete'; [key: string]: unknown };
  session_error: { type: 'session_error'; message: string; recoverable: boolean };
  transcript: { type: 'transcript'; text: string };
  skill_fired: { type: 'skill_fired'; skillId: string; triggerType: string; actions: string[] };
  skill_escalated: { type: 'skill_escalated'; skillId: string; escalationLevel: string; context: unknown };
  skill_conflict: { type: 'skill_conflict'; skillIds: string[]; winner: string; resolution: string };
  skill_registered: { type: 'skill_registered'; skillId: string; source: string; triggerType: string };
  skill_removed: { type: 'skill_removed'; skillId: string };
  skill_updated: { type: 'skill_updated'; skillId: string; patch: Record<string, unknown> };
  pack_loaded: { type: 'pack_loaded'; packName: string; skillCount: number };
  pack_unloaded: { type: 'pack_unloaded'; packName: string };
  event_mapping_added: { type: 'event_mapping_added'; mappingId: string; source: string; eventName: string };
  event_mapping_removed: { type: 'event_mapping_removed'; mappingId: string };
  sensor_update: { type: 'sensor_update'; temperature: number | null; humidity: number | null; pressure: number | null };
  counter_update: { type: 'counter_update'; counters: Record<string, number> };
}

export type SSEEvent = SSEEventMap[keyof SSEEventMap];
```

## Implementation

### Step 1: Make `broadcastSSE` public (Expansion 2.1)

**File:** `harness/src/comms/ControlServer.ts`

Rename the public method:

```typescript
// Before:
private broadcastSSE(data: object): void { /* ... iterates clients ... */ }
public broadcastSkillEvent(data: object): void { this.broadcastSSE(data); }

// After:
public broadcastSSE(data: SSEEvent): void {
  /* ... iterates clients ... */
}
// Remove broadcastSkillEvent — all callers use broadcastSSE directly
```

Update all callers in `core.ts`:
```typescript
// Before: controlServer.broadcastSkillEvent({ type: 'skill_fired', ...event });
// After:  controlServer.broadcastSSE({ type: 'skill_fired', ...event });
```

### Step 2: Add EventEmitter events to SpaceManager

**File:** `harness/src/engine/SpaceManager.ts`

Currently, SpaceManager emits `skill_fired`, `skill_escalated`, `skill_conflict` via `broadcastObservabilityEvent()`. Add new lifecycle events:

```typescript
// In registerSkill(), after skill is added:
this.emit('skill_registered', { skillId: skill.id, source: skill.source, triggerType: skill.trigger.type });

// In removeSkill(), before skill is removed:
this.emit('skill_removed', { skillId });

// In updateSkill(), after patch is applied:
this.emit('skill_updated', { skillId, patch });

// In disableSkill(), after enabled state is toggled:
this.emit('skill_updated', { skillId, patch: { enabled } });
```

### Step 3: Add EventEmitter events to PackLoader

**File:** `harness/src/engine/PackLoader.ts`

PackLoader currently extends nothing (no EventEmitter). Add `extends EventEmitter` and emit events:

```typescript
import { EventEmitter } from 'events';

export class PackLoader extends EventEmitter {
  // In loadPack(), after all skills are registered:
  this.emit('pack_loaded', { packName, skillCount: parsed.skills.length });

  // In unloadCurrentPack(), after all skills are removed:
  this.emit('pack_unloaded', { packName: this.loadedPack! });
}
```

### Step 4: Add `mode_change` event to ModeManager (Expansion 5.5)

**File:** `harness/src/engine/ModeManager.ts`

ModeManager already tracks transitions. Add an event emission for mode history:

```typescript
// In the method that handles mode transitions (after validation):
this.emit('mode_change', { from: previousMode, to: newMode, timestamp: Date.now() });
```

Wire in core.ts:
```typescript
modeManager.on('mode_change', (data) => {
  controlServer.broadcastSSE({ type: 'mode_change', ...data });
});
```

### Step 5: Add `getCounters()` to SkillExecutor

**File:** `harness/src/engine/SkillExecutor.ts`

Add a public getter for counter state:

```typescript
getCounters(): Record<string, number> {
  return Object.fromEntries(this.counters);
}
```

Expose via SpaceManager:

```typescript
// SpaceManager.ts
getCounters(spaceId?: string): Record<string, number> {
  const executor = spaceId
    ? this.executors.get(spaceId)
    : this.executors.values().next().value;
  return executor?.getCounters() ?? {};
}
```

### Step 6: Add throttled SSE broadcaster

**File:** `harness/src/comms/ControlServer.ts`

Add throttling in ControlServer for sensor and counter events:

```typescript
private sensorThrottleTimer: NodeJS.Timeout | null = null;
private lastSensorBroadcast = 0;
private counterThrottleTimer: NodeJS.Timeout | null = null;
private lastCounterBroadcast = 0;
private static THROTTLE_MS = 1000; // 1 second

private broadcastThrottledSensor(data: object): void {
  const now = Date.now();
  if (now - this.lastSensorBroadcast >= ControlServer.THROTTLE_MS) {
    this.lastSensorBroadcast = now;
    this.broadcastSSE({ type: 'sensor_update', ...data });
  } else if (!this.sensorThrottleTimer) {
    this.sensorThrottleTimer = setTimeout(() => {
      this.sensorThrottleTimer = null;
      this.lastSensorBroadcast = Date.now();
      this.broadcastSSE({ type: 'sensor_update', ...data });
    }, ControlServer.THROTTLE_MS - (now - this.lastSensorBroadcast));
  }
}
```

### Step 7: Counter interval optimization (Expansion 2.2)

The 1s interval polls counters even when no skills have collectors, firing 86,400 times/day doing nothing. **Optimization:** Only start the interval when the first counter-using skill is registered, and clear it when the last one is removed.

```typescript
// In core.ts:
private counterInterval: NodeJS.Timeout | null = null;

spaceManager.on('skill_registered', (data) => {
  controlServer.broadcastSSE({ type: 'skill_registered', ...data });
  // Start counter polling if this skill has collectors
  const skill = spaceManager.listSkills().find(s => s.id === data.skillId);
  if (skill?.collect?.length && !this.counterInterval) {
    this.startCounterPolling();
  }
});

spaceManager.on('skill_removed', (data) => {
  controlServer.broadcastSSE({ type: 'skill_removed', ...data });
  // Stop counter polling if no skills have collectors
  const hasCollectors = spaceManager.listSkills().some(s => s.collect?.length);
  if (!hasCollectors && this.counterInterval) {
    clearInterval(this.counterInterval);
    this.counterInterval = null;
  }
});

private startCounterPolling(): void {
  this.counterInterval = setInterval(() => {
    const counters = spaceManager.getCounters();
    controlServer.broadcastSSE({ type: 'counter_update', counters });
  }, 1000);
}
```

### Step 8: Wire new events in core.ts

**File:** `harness/src/core.ts`

```typescript
// Skill lifecycle events
spaceManager.on('skill_registered', (data) => {
  controlServer.broadcastSSE({ type: 'skill_registered', ...data });
});
spaceManager.on('skill_removed', (data) => {
  controlServer.broadcastSSE({ type: 'skill_removed', ...data });
});
spaceManager.on('skill_updated', (data) => {
  controlServer.broadcastSSE({ type: 'skill_updated', ...data });
});

// Pack events
packLoader.on('pack_loaded', (data) => {
  controlServer.broadcastSSE({ type: 'pack_loaded', ...data });
});
packLoader.on('pack_unloaded', (data) => {
  controlServer.broadcastSSE({ type: 'pack_unloaded', ...data });
});

// Event mapping events
eventBridge.on('mappingAdded', (data) => {
  controlServer.broadcastSSE({ type: 'event_mapping_added', ...data });
});
eventBridge.on('mappingRemoved', (data) => {
  controlServer.broadcastSSE({ type: 'event_mapping_removed', mappingId: data });
});

// Mode change events (Expansion 5.5)
modeManager.on('mode_change', (data) => {
  controlServer.broadcastSSE({ type: 'mode_change', ...data });
});

// Throttled sensor updates (reuse existing MQTT sensor handler)
// Replace direct broadcastSSE with broadcastThrottledSensor
```

## Files Changed

| File | Action | Description |
|---|---|---|
| `harness/src/comms/ControlServer.ts` | MODIFY | Make `broadcastSSE` public, add throttled broadcast methods |
| `harness/src/comms/sse-types.ts` | NEW | SSE event type definitions (Expansion 2.4) |
| `harness/src/engine/SpaceManager.ts` | MODIFY | Add lifecycle event emissions (skill_registered/removed/updated) |
| `harness/src/engine/PackLoader.ts` | MODIFY | Extend EventEmitter, add pack_loaded/pack_unloaded events |
| `harness/src/engine/SkillExecutor.ts` | MODIFY | Add `getCounters()` public method |
| `harness/src/engine/ModeManager.ts` | MODIFY | Add `mode_change` event emission |
| `harness/src/core.ts` | MODIFY | Wire lifecycle events → ControlServer SSE, counter interval optimization |

## Verification

1. `npx tsc --noEmit` — Zero type errors
2. `npx vitest run` — All tests pass
3. Register a skill via REST → SSE client receives `skill_registered` event within 1 second
4. Remove a skill → SSE client receives `skill_removed` event
5. Load a pack → SSE client receives `pack_loaded` event
6. Sensor update arrives → SSE client receives throttled `sensor_update` (max 1/second)
7. Counter update → SSE client receives `counter_update` (only when counter-using skills exist)
8. Mode transition → SSE client receives `mode_change` event with `{ from, to, timestamp }`
9. Remove all counter-using skills → counter polling interval is cleared (no CPU waste)
10. Register first counter-using skill → counter polling interval starts

## Edge Cases

- **SSE client connects mid-stream:** Client receives `connected` event, then must fetch REST state for initial render. New lifecycle events only fire going forward.
- **Multiple SSE clients:** `broadcastSSE` iterates all clients; throttling is per-server (not per-client), so all clients get the same throttled rate.
- **PackLoader events with no listeners:** EventEmitter default is 10 listeners; if more are added, increase with `packLoader.setMaxListeners(20)`.
- **Counter interval lifecycle:** Interval starts on first `skill_registered` with `collect`, stops on last `skill_removed` with `collect`. Edge: what if a skill's collect is PATCHed in? SpaceManager should emit `skill_updated` with patch containing `collect` — core.ts checks if collect was added/removed.
- **`broadcastSSE` rename:** All existing callers in core.ts must be updated from `broadcastSkillEvent` to `broadcastSSE`. Missing update causes compile error (type-safe).

---
*Plan: 08-02 | Phase: 8 | Wave: 1 (backend) | Depends: 08-07*
