daviddatuX25/Xentient/.planning/phases/08-web-console-dashboard/08-03-PLAN.md

---
plan: 08-03
title: Dashboard Overview Panel
phase: 8
wave: 2 (frontend)
depends_on: [08-01, 08-02]
hard_points: [H6]
estimated_files: 8
estimated_loc: 800
---

# 08-03: Dashboard Overview Panel

## Goal

Build the main landing page of the Xentient Web Console showing system health at a glance: mode status, MQTT/camera/brain connectivity, live sensor gauges, active skills summary, and quick action buttons.

## Prerequisites

- **08-01 complete** — REST endpoints available
- **08-02 complete** — SSE events flowing

## Architecture Decision

Single-page HTML/JS dashboard served as static files from `public/`. No framework (React/Vue/Svelte). Vanilla JS + CSS using ES modules. No build step needed — `<script type="module" src="/js/main.js">` works natively in all modern browsers.

## Design System & Execution

**Design Reference:** `docs/xai-DESIGN.md`
**Execution Skill:** Use the `frontend-design` skill for all CSS implementation.

### Token Mapping:

| Token | Value | Usage |
|---|---|---|
| `--bg-primary` | `#1f2228` | Page background, panel backgrounds |
| `--bg-deep` | `#0a0a0a` | Overlays, deep layers, drawer backdrop |
| `--text-primary` | `#ffffff` | Headings, labels, primary content |
| `--text-secondary` | `#7d8187` | Hints, timestamps, muted content |
| `--accent` | `#2563eb` | Interactive elements, links, active states |
| `--border` | `#0c0c0b` | Subtle dividers, card borders |
| `--font-ui` | `universalSans, -apple-system, system-ui, sans-serif` | All UI text |
| `--font-mono` | `GeistMono, ui-monospace, monospace` | Skill IDs, sensor values, timestamps |
| `--radius-pill` | `9999px` | Primary action buttons |
| `--radius-card` | `24px` | Card containers |
| `--weight` | `400` | All text — no bold, hierarchy via size only |

### Mode badge colors (override per-mode):
| Mode | Color |
|---|---|
| sleep | `hsl(240, 60%, 55%)` (indigo) |
| listen | `hsl(160, 60%, 45%)` (emerald) |
| active | `hsl(40, 90%, 50%)` (amber) |
| record | `hsl(0, 70%, 55%)` (red) |

These mode colors are **exceptions** to the accent-blue-only rule — they are status indicators, not interactive elements.

### Elevation & Depth:
- Use gradient backgrounds and transparency for depth, NOT box-shadows
- Cards: `background: rgba(31, 34, 40, 0.7); backdrop-filter: blur(12px);`
- Use `border: 1px solid rgba(255,255,255,0.06)` for subtle card edges

### Font Loading (Expansion 3.3)

`universalSans` and `GeistMono` are not system fonts. Self-host WOFF2 files:

```html
<!-- In index.html <head> -->
<link rel="preload" href="/fonts/universalSans-Regular.woff2" as="font" type="font/woff2" crossorigin>
<link rel="preload" href="/fonts/GeistMono-Regular.woff2" as="font" type="font/woff2" crossorigin>
```

```css
/* In dashboard.css */
@font-face {
  font-family: 'universalSans';
  src: url('/fonts/universalSans-Regular.woff2') format('woff2');
  font-weight: 400;
  font-display: swap;
}
@font-face {
  font-family: 'GeistMono';
  src: url('/fonts/GeistMono-Regular.woff2') format('woff2');
  font-weight: 400;
  font-display: swap;
}
```

Fallback stack: `universalSans, -apple-system, system-ui, sans-serif` and `GeistMono, ui-monospace, monospace`. Fonts load async via `font-display: swap`.

## ES Module Architecture (Expansion C3)

Split dashboard into ES modules to prevent a single unmaintainable `dashboard.js` file. No build step — native ES modules work in all modern browsers:

```
harness/public/
├── index.html
├── dashboard.css
├── fonts/
│   ├── universalSans-Regular.woff2
│   └── GeistMono-Regular.woff2
└── js/
    ├── main.js          (init, state, tab routing, hash routing)
    ├── api.js           (REST API client)
    ├── sse.js           (SSE client + reconnection)
    ├── overview.js      (overview panel)
    ├── skills.js        (skill manager panel — 08-04)
    ├── telemetry.js     (sparklines, event feed — 08-05)
    ├── mode.js          (mode + space controls — 08-06)
    └── components.js    (toast, skeleton, gauge, badge)
```

## Implementation

### Step 1: Create dashboard SPA shell

**File:** `harness/public/index.html` (NEW, replaces test.html as root)

```html
<!DOCTYPE html>
<html lang="en">
<head>
  <meta charset="UTF-8">
  <meta name="viewport" content="width=device-width, initial-scale=1.0">
  <title>Xentient</title>
  <link rel="preload" href="/fonts/universalSans-Regular.woff2" as="font" type="font/woff2" crossorigin>
  <link rel="preload" href="/fonts/GeistMono-Regular.woff2" as="font" type="font/woff2" crossorigin>
  <link rel="stylesheet" href="/dashboard.css">
</head>
<body>
  <div id="app">
    <header id="header"><!-- mode badge + connection status --></header>
    <nav id="nav"><!-- tab bar: Overview, Skills, Telemetry, Mode --></nav>
    <main id="content"><!-- panel content --></main>
  </div>
  <div id="reconnect-banner" class="banner hidden">Reconnecting...</div>
  
  <script type="module" src="/js/main.js"></script>
</body>
</html>
```

**Key design decisions:**
- Tab navigation (Overview / Skills / Telemetry / Mode) — only one panel visible at a time
- Header shows current mode badge + connection indicators
- `reconnect-banner` appears when SSE disconnects
- `toast-container` for error/info notifications
- Page title updates to show current mode: "Xentient — listen"
- `type="module"` enables ES module imports natively

### Step 2: Create CSS file

**File:** `harness/public/dashboard.css` (NEW)

Uses xai-DESIGN.md tokens (NOT GitHub Dark):

```css
:root {
  --bg-primary: #1f2228;
  --bg-deep: #0a0a0a;
  --text-primary: #ffffff;
  --text-secondary: #7d8187;
  --accent: #2563eb;
  --border: #0c0c0b;
  --font-ui: universalSans, -apple-system, system-ui, sans-serif;
  --font-mono: GeistMono, ui-monospace, monospace;
  --radius-pill: 9999px;
  --radius-card: 24px;
  --weight: 400;
  --mode-sleep: hsl(240, 60%, 55%);
  --mode-listen: hsl(160, 60%, 45%);
  --mode-active: hsl(40, 90%, 50%);
  --mode-record: hsl(0, 70%, 55%);
}
```

- Dark theme using `--bg-primary: #1f2228` (NOT `#0d1117` — that's GitHub Dark, not Xentient)
- Glassmorphism cards: `background: rgba(31, 34, 40, 0.7); backdrop-filter: blur(12px); border: 1px solid rgba(255,255,255,0.06);`
- NO box-shadows — elevation via gradient overlays + transparency
- Pill-shaped buttons (9999px radius) for CTAs, 24px radius for cards
- Font weight: 400 only — hierarchy via size + letter-spacing
- Responsive CSS Grid with breakpoints: mobile (<768px) single column, desktop multi-column

### Step 3: Create main.js — state, routing, init

**File:** `harness/public/js/main.js` (NEW)

```javascript
import { DashboardAPI } from './api.js';
import { DashboardSSE } from './sse.js';
import { renderOverview } from './overview.js';
import { showToast } from './components.js';

// ─── State Management ───────────────────────────────
export const state = {
  mode: 'sleep',
  mqtt: false,
  camera: { online: false },
  brain: false,
  sensors: { temperature: null, humidity: null, pressure: null, motion: null, lastMotionAt: null },
  skills: [],
  activePack: null,
  connected: false,
  activeTab: 'overview',
};

// ─── Tab Routing (Expansion 3.6) ─────────────────────
// Hash-based routing enables deep linking, browser back/forward, bookmarkable state
const TABS = ['overview', 'skills', 'telemetry', 'mode'];

function setActiveTab(tab) {
  if (!TABS.includes(tab)) tab = 'overview';
  state.activeTab = tab;
  window.location.hash = tab;
  renderActivePanel();
  // Update nav active state
  document.querySelectorAll('#nav button').forEach(b => b.classList.toggle('active', b.dataset.tab === tab));
}

window.addEventListener('hashchange', () => {
  const hash = window.location.hash.slice(1);
  if (TABS.includes(hash)) setActiveTab(hash);
});

function renderActivePanel() {
  const content = document.getElementById('content');
  switch (state.activeTab) {
    case 'overview': renderOverview(content, state, api); break;
    // Skills, Telemetry, Mode panels added in 08-04, 08-05, 08-06
    default: content.innerHTML = '<p>Panel not yet implemented</p>';
  }
}

// ─── Init ────────────────────────────────────────────
const api = new DashboardAPI();
const sse = new DashboardSSE();

async function init() {
  // Show skeleton placeholders (Expansion 3.7)
  document.getElementById('content').innerHTML = renderOverviewSkeleton();

  // Fetch initial state from REST endpoints
  const [status, sensors, skills, packs, config] = await Promise.all([
    api.getStatus(),
    api.getSensors(),
    api.getSkills(),
    api.getPacks(),
    api.getConfig(),
  ]);
  Object.assign(state, status, { skills, activePack: packs.loaded, config });

  // Set initial tab from hash or default
  const hash = window.location.hash.slice(1);
  setActiveTab(TABS.includes(hash) ? hash : 'overview');

  // Connect SSE for real-time updates
  sse.connect();
}

init();
```

### Step 4: Overview Panel Components

| Component | Data Source | Update |
|---|---|---|
| **System Status Card** | `/api/status` | SSE `mode_status` |
| ├─ Mode badge | `modeManager.getMode()` | Real-time via SSE |
| ├─ MQTT connected | `status.mqtt` | SSE `mode_status` |
| ├─ Camera online/offline | `status.camera` | Poll every 10s |
| └─ Brain connected | `getBrainConnected()` | SSE `mode_status` |
| **Sensor Gauges** | `/api/sensors` | SSE `sensor_update` |
| ├─ Temperature gauge (°C) | `sensors.temperature` | Circular progress, smooth transition |
| ├─ Humidity gauge (%) | `sensors.humidity` | Circular progress, smooth transition |
| └─ Motion indicator | `sensors.motion` | Last triggered timestamp |
| **Active Skills Summary** | `/api/skills` | SSE `skill_registered/removed/updated` |
| ├─ Total / enabled / disabled | `skills.length` counts | On change |
| ├─ Skills fired (last 5 min) | `/api/skill-log?since=5m` | Poll every 30s |
| └─ Active pack name | `/api/packs` | SSE `pack_loaded` |
| **Quick Actions** | POST endpoints | Click |
| ├─ Mode switch buttons (4) | `/api/mode` | Loading state → SSE confirm |
| ├─ Trigger pipeline button | `/api/trigger` | Loading state → SSE confirm |
| └─ Reload pack button | `/api/packs/default/reload` | Loading state → SSE confirm |

### Step 5: Gauge component — SVG with sensor ranges (Expansion 3.4)

Each sensor gauge has specific min/max ranges:

| Sensor | Min | Max | Unit |
|---|-----|-----|---|
| Temperature | 0 | 50 | °C |
| Humidity | 0 | 100 | % |
| Pressure | 900 | 1100 | hPa |

```html
<div class="gauge" data-value="23.5" data-min="0" data-max="50" data-unit="°C">
  <svg viewBox="0 0 100 100">
    <circle class="gauge-bg" cx="50" cy="50" r="42" />
    <circle class="gauge-fill" cx="50" cy="50" r="42" />
  </svg>
  <span class="gauge-value">23.5</span>
  <span class="gauge-label">Temperature</span>
</div>
```

`stroke-dashoffset` calculation:
```javascript
const CIRCUMFERENCE = 2 * Math.PI * 42; // ≈ 263.9
const ratio = Math.max(0, Math.min(1, (value - min) / (max - min)));
const offset = CIRCUMFERENCE * (1 - ratio);
circle.style.strokeDashoffset = offset;
```

### Step 6: Quick action button feedback (Expansion 3.5)

When user clicks a quick action button, show immediate feedback before SSE confirmation:

1. Button enters **loading state**: disabled + spinner icon, text changes to "Switching..."
2. API responds (success or error)
3. If success: SSE confirms within ~200ms, button returns to normal
4. If error: show toast with error message, button returns to normal
5. **Timeout guard:** If no SSE confirmation within 5s, button returns to normal anyway (SSE might have missed it)

```javascript
async function handleQuickAction(btn, apiCall) {
  const original = btn.textContent;
  btn.disabled = true;
  btn.innerHTML = `<span class="spinner"></span> ${original}...`;

  try {
    await apiCall();
  } catch (err) {
    showToast(`Error: ${err.message}`, 'error');
  } finally {
    // SSE will update the state, but restore button after 2s max
    setTimeout(() => {
      btn.disabled = false;
      btn.textContent = original;
    }, 2000);
  }
}
```

### Step 7: Initial loading skeleton (Expansion 3.7)

Skeleton placeholders appear on first load while REST fetches complete:

```javascript
function renderOverviewSkeleton() {
  return `
    <div class="skeleton-card">

    </div>
    <div class="skeleton-gauges">

    </div>
  `;
}
```

```css
.skeleton-line { height: 16px; background: rgba(125, 129, 135, 0.15); border-radius: 4px; margin-bottom: 8px; }
.skeleton-circle { width: 120px; height: 120px; border-radius: 50%; background: rgba(125, 129, 135, 0.1); }
.w-40 { width: 40%; }
.w-60 { width: 60%; }
```

### Step 8: SSE Reconnection + State Recovery

On SSE connect, fetch all REST endpoints for initial state. On reconnect:

```javascript
sse.on('connected', () => {
  // Re-fetch full state on reconnect
  api.getStatus().then(s => { state.mode = s.mode; state.mqtt = s.mqtt; });
  api.getSkills().then(s => { state.skills = s; });
  // ... etc
  renderActivePanel();
});
```

### Step 9: Update ControlServer static file serving

In `ControlServer.serveStatic()`, update default route to serve `index.html` instead of `test.html`:

```typescript
// Before: if (url === '/') url = '/test.html';
// After:
if (url === '/') url = '/index.html';
```

Keep `test.html` accessible at `/test.html` for backward compatibility.

## Files Changed

| File | Action | Description |
|---|---|---|
| `harness/public/index.html` | NEW | SPA shell with ES module script, font preloading |
| `harness/public/dashboard.css` | NEW | xai-DESIGN.md tokens, glassmorphism, responsive grid |
| `harness/public/fonts/universalSans-Regular.woff2` | NEW | Self-hosted font file |
| `harness/public/fonts/GeistMono-Regular.woff2` | NEW | Self-hosted font file |
| `harness/public/js/main.js` | NEW | Init, state, hash routing, tab switching |
| `harness/public/js/api.js` | NEW | REST API client module |
| `harness/public/js/sse.js` | NEW | SSE client + reconnection module |
| `harness/public/js/overview.js` | NEW | Overview panel renderer |
| `harness/public/js/components.js` | NEW | Toast, skeleton, gauge, badge components |
| `harness/src/comms/ControlServer.ts` | MODIFY | Default route serves index.html |

## Verification

1. `http://localhost:3000/` loads the dashboard
2. Mode badge shows current mode with correct xai-DESIGN.md colors
3. CSS custom properties match `xai-DESIGN.md` tokens exactly (no GitHub Dark colors)
4. MQTT status indicator reflects connection state
5. Sensor gauges update within 1s of SSE `sensor_update`
6. Clicking "Listen" mode button → loading state → badge changes to emerald "LISTEN" within 200ms
7. Active skills count matches `/api/skills` response
8. Quick actions show loading state, then confirm via SSE
9. Dashboard works on mobile (375px width viewport)
10. SSE disconnect → "Reconnecting..." banner appears → reconnect → banner disappears, state recovers
11. Page title updates: "Xentient — listen" when mode changes
12. Hash routing works: `#overview`, `#skills`, `#telemetry`, `#mode` — browser back/forward works
13. Skeleton placeholders show during initial load
14. Font loading: universalSans renders first with system-ui fallback, swaps when loaded
15. All text uses weight 400 — no bold anywhere

## Edge Cases

- **Font files missing:** Fallback stack renders with system-ui. No layout shift if `font-display: swap` is used.
- **SSE reconnect during action:** If user clicks "Trigger Pipeline" and SSE reconnects mid-request, the button loading state times out after 2s and state is re-fetched.
- **Hash routing with unknown hash:** Falls back to `#overview`.
- **Module loading failure:** If any ES module fails to load, `import` will throw. Wrap `init()` in try/catch, show error toast.

---
*Plan: 08-03 | Phase: 8 | Wave: 2 (frontend) | Depends: 08-01, 08-02*
