daviddatuX25/Xentient/.planning/phases/08-web-console-dashboard/08-05-PLAN.md

---
plan: 08-05
title: Live Telemetry & Event Feed
phase: 8
wave: 2 (frontend)
depends_on: [08-01, 08-02]
hard_points: [H4, H7, H8]
estimated_files: 5
estimated_loc: 550
---

# 08-05: Live Telemetry & Event Feed

## Goal

Build the telemetry panel with real-time sensor sparklines, motion timeline, skill fire log, escalation feed, conflict log, and mode timeline. Also implements the `SensorHistory`, `MotionHistory`, and `ModeHistory` ring buffers on the server side.

## Prerequisites

- **08-01 complete** — `/api/sensors/history` endpoint, `/api/skill-log` endpoint
- **08-02 complete** — `sensor_update`, `mode_change` SSE events

## Design System & Execution

**Design Reference:** `docs/xai-DESIGN.md`
**Execution Skill:** Use the `frontend-design` skill for all CSS implementation.

### Token Mapping:

| Token | Value | Usage |
|---|---|---|
| `--bg-primary` | `#1f2228` | Page background, panel backgrounds |
| `--bg-deep` | `#0a0a0a` | Overlays, deep layers |
| `--text-primary` | `#ffffff` | Headings, labels, primary content |
| `--text-secondary` | `#7d8187` | Hints, timestamps, muted content |
| `--accent` | `#2563eb` | Interactive elements, sparkline accent |
| `--border` | `#0c0c0b` | Subtle dividers |
| `--font-mono` | `GeistMono, ui-monospace, monospace` | Sensor values, timestamps, skill IDs |
| `--radius-card` | `24px` | Card containers |
| `--weight` | `400` | All text |

### Mode badge colors for timeline:
| Mode | Color |
|---|---|
| sleep | `hsl(240, 60%, 55%)` (indigo) |
| listen | `hsl(160, 60%, 45%)` (emerald) |
| active | `hsl(40, 90%, 50%)` (amber) |
| record | `hsl(0, 70%, 55%)` (red) |

### Sparkline colors:
| Sensor | Color |
|---|---|
| Temperature | `hsl(40, 90%, 50%)` (amber) |
| Humidity | `hsl(160, 60%, 45%)` (emerald) |
| Pressure | `hsl(240, 60%, 55%)` (indigo) |

NOT hardcoded hex values — uses xai-DESIGN.md mode color palette.

## Hard Points Addressed

- **H4**: Sparkline rendering without charting library → Canvas with retina DPI handling + rolling array
- **H7**: Historical data for sparklines on first load → `/api/sensors/history` endpoint seeded from ring buffer
- **H8**: Sensor history ring buffer → `SensorHistory` class in Core

## Implementation

### Step 1: Create SensorHistory ring buffer

**File:** `harness/src/engine/SensorHistory.ts` (NEW, ~60 lines)

```typescript
export interface SensorReading {
  temperature: number | null;
  humidity: number | null;
  pressure: number | null;
  timestamp: number; // Unix epoch ms
}

export class SensorHistory {
  private buffer: SensorReading[] = [];
  private maxEntries: number;
  private lastPushTime = 0;
  private intervalMs: number;

  constructor(maxEntries = 300, intervalMs = 1000) {
    this.maxEntries = maxEntries;
    this.intervalMs = intervalMs;
  }

  push(reading: SensorReading): void {
    const now = Date.now();
    if (now - this.lastPushTime < this.intervalMs) return; // Throttle: 1 entry/second
    this.lastPushTime = now;
    this.buffer.push({ ...reading, timestamp: now });
    if (this.buffer.length > this.maxEntries) this.buffer.shift();
  }

  query(sinceMs?: number): SensorReading[] {
    if (!sinceMs) return [...this.buffer];
    const cutoff = Date.now() - sinceMs;
    return this.buffer.filter(r => r.timestamp >= cutoff);
  }

  clear(): void {
    this.buffer = [];
  }
}
```

### Step 2: Create MotionHistory ring buffer (Expansion 5.4)

The motion timeline needs a history of PIR events. `sensorCache.motion` is only a boolean (last state). Create a ring buffer:

**File:** `harness/src/engine/MotionHistory.ts` (NEW, ~40 lines)

```typescript
export interface MotionEvent {
  timestamp: number;
  active: boolean; // true = motion detected, false = motion cleared
}

export class MotionHistory {
  private buffer: MotionEvent[] = [];
  private maxEntries = 180; // 30 minutes at 10s intervals

  push(active: boolean): void {
    this.buffer.push({ timestamp: Date.now(), active });
    if (this.buffer.length > this.maxEntries) this.buffer.shift();
  }

  query(sinceMs?: number): MotionEvent[] {
    if (!sinceMs) return [...this.buffer];
    const cutoff = Date.now() - sinceMs;
    return this.buffer.filter(e => e.timestamp >= cutoff);
  }
}
```

Wire into core.ts: When MQTT motion message arrives, push to `motionHistory`.

Add endpoint: `GET /api/sensors/motion-history?minutes=30`

```typescript
private async handleGetMotionHistory(req: IncomingMessage, res: ServerResponse): Promise<void> {
  const url = new URL(req.url!, 'http://localhost');
  const minutes = Number(url.searchParams.get('minutes') ?? '30');
  const sinceMs = minutes * 60 * 1000;
  const history = this.deps.motionHistory.query(sinceMs);
  this.sendJSON(res, 200, history);
}
```

### Step 3: Create ModeHistory ring buffer (Expansion 5.5)

Mode timeline needs a list of `{mode, startTime, endTime}` intervals. Record mode transitions:

**File:** `harness/src/engine/ModeHistory.ts` (NEW, ~50 lines)

```typescript
export interface ModeInterval {
  mode: string;
  startTime: number;
  endTime: number | null; // null = current mode (still active)
}

export class ModeHistory {
  private intervals: ModeInterval[] = [];
  private maxIntervals = 100;
  private currentMode: string | null = null;
  private currentStart: number = 0;

  recordTransition(mode: string): void {
    const now = Date.now();
    // Close previous interval
    if (this.currentMode) {
      this.intervals.push({ mode: this.currentMode, startTime: this.currentStart, endTime: now });
    }
    // Start new interval
    this.currentMode = mode;
    this.currentStart = now;
    // Trim old entries
    if (this.intervals.length > this.maxIntervals) this.intervals.shift();
  }

  query(sinceMs?: number): ModeInterval[] {
    const result = sinceMs
      ? this.intervals.filter(i => i.endTime === null || i.endTime >= Date.now() - sinceMs)
      : [...this.intervals];
    // Add current mode as open interval
    if (this.currentMode) {
      result.push({ mode: this.currentMode, startTime: this.currentStart, endTime: null });
    }
    return result;
  }
}
```

Wire into core.ts: Listen to `modeManager.on('mode_change', ...)` and call `modeHistory.recordTransition(to)`.

Add endpoint: `GET /api/mode/history?minutes=30`

```typescript
private async handleGetModeHistory(req: IncomingMessage, res: ServerResponse): Promise<void> {
  const url = new URL(req.url!, 'http://localhost');
  const minutes = Number(url.searchParams.get('minutes') ?? '30');
  const sinceMs = minutes * 60 * 1000;
  const history = this.deps.modeHistory.query(sinceMs);
  this.sendJSON(res, 200, history);
}
```

### Step 4: Wire history classes into core.ts and ControlServerDeps

**File:** `harness/src/core.ts` (MODIFY)

```typescript
const sensorHistory = new SensorHistory();
const motionHistory = new MotionHistory();
const modeHistory = new ModeHistory();

// In MQTT sensor handler, after updating sensorCache:
sensorHistory.push(sensorCache);

// In MQTT motion handler:
motionHistory.push(sensorCache.motion);

// Wire mode change → modeHistory
modeManager.on('mode_change', (data) => {
  modeHistory.recordTransition(data.to);
  controlServer.broadcastSSE({ type: 'mode_change', ...data });
});

// Add to ControlServerDeps:
const deps: ControlServerDeps = {
  // ... existing ...
  sensorHistory,
  motionHistory,
  modeHistory,
};
```

Update `ControlServerDeps` interface to include `motionHistory` and `modeHistory`.

### Step 5: Sparkline rendering — Canvas with retina DPI (Expansion 5.2)

**File:** `harness/public/js/telemetry.js` (NEW ES module)

```javascript
export class Sparkline {
  constructor(canvasId, maxPoints = 200) {
    this.canvas = document.getElementById(canvasId);
    this.ctx = this.canvas.getContext('2d');
    this.data = [];
    this.maxPoints = maxPoints;
    this.setupDPI();
  }

  setupDPI() {
    const dpr = window.devicePixelRatio || 1;
    const rect = this.canvas.getBoundingClientRect();
    this.canvas.width = rect.width * dpr;
    this.canvas.height = rect.height * dpr;
    this.ctx.scale(dpr, dpr);
    this.canvas.style.width = rect.width + 'px';
    this.canvas.style.height = rect.height + 'px';
  }

  seed(values) {
    this.data = values.slice(-this.maxPoints);
    this.draw();
  }

  push(value) {
    this.data.push(value);
    if (this.data.length > this.maxPoints) this.data.shift();
    this.draw();
  }

  draw() {
    const { ctx, data } = this;
    const w = this.canvas.clientWidth;
    const h = this.canvas.clientHeight;
    ctx.clearRect(0, 0, w, h);

    if (data.length < 2) return;

    const min = Math.min(...data);
    const max = Math.max(...data);
    const range = max - min;

    // Flat-line centering (Expansion 5.3)
    // If all values are identical, center the line vertically
    const step = w / (this.maxPoints - 1);

    ctx.beginPath();
    ctx.strokeStyle = getComputedStyle(this.canvas).getPropertyValue('--sparkline-color') || 'hsl(160, 60%, 45%)';
    ctx.lineWidth = 1.5;

    for (let i = 0; i < data.length; i++) {
      const x = i * step;
      let y;
      if (range === 0) {
        y = h / 2; // Center flat line vertically
      } else {
        y = h - ((data[i] - min) / range) * (h - 4) - 2;
      }
      if (i === 0) ctx.moveTo(x, y);
      else ctx.lineTo(x, y);
    }
    ctx.stroke();
  }
}
```

### Step 6: Telemetry Panel Components

| Component | Implementation | Data Source |
|---|---|---|
| **Temperature Sparkline** | Canvas `<canvas id="spark-temp">`, 200-point rolling window | `/api/sensors/history?minutes=5` on load, then SSE `sensor_update` |
| **Humidity Sparkline** | Canvas `<canvas id="spark-hum">` | Same |
| **Pressure Sparkline** | Canvas `<canvas id="spark-press">` | Same |
| **Motion Timeline** | Horizontal bar, 30min window, dots for PIR events | `/api/sensors/motion-history?minutes=30` on load, then SSE `sensor_update` |
| **Skill Fire Log** | Reverse-chronological list, max 100 entries | `/api/skill-log?limit=100` on load, then SSE `skill_fired` |
| **Escalation Feed** | Color-coded cards (critical=red, high=amber, normal=accent-blue) | SSE `skill_escalated` |
| **Conflict Log** | Shows conflicting skills, resolution, winner | SSE `skill_conflict` |
| **Mode Timeline** | Horizontal bar, color-coded blocks per mode interval | `/api/mode/history?minutes=30` on load, then SSE `mode_change` |

### Step 7: Escalation Feed — Context Snapshot Rendering (Expansion 5.6)

SkillEscalationEvent's context is built by `buildContext()` which returns sensor data, counters, mode history, and optional camera frame. For v1:

- **Skip camera frame** — no base64 JPEG thumbnail in dashboard
- **Show JSON of sensor + counter context** in a collapsible `<details>` element

```html
<div class="escalation-card">
  <div class="escalation-header">
    <span class="escalation-level critical">CRITICAL</span>
    <span class="skill-id">_pir-wake</span>
    <span class="timestamp">14:45:03</span>
  </div>
  <details class="escalation-context">
    <summary>Context</summary>
    <pre class="context-json">{
  "sensors": { "temperature": 23.5, "motion": true },
  "counters": { "pir_count": 42 },
  "mode": "listen"
}</pre>
  </details>
</div>
```

### Step 8: First-load data seeding

On dashboard init and on SSE reconnect:

```javascript
export async function seedTelemetryData(api) {
  const [sensorHistory, motionHistory, modeHistory, skillLog] = await Promise.all([
    api.getSensorHistory(5),
    api.getMotionHistory(30),
    api.getModeHistory(30),
    api.getSkillLog({ limit: 100 }),
  ]);

  sparkTemp.seed(sensorHistory.map(r => r.temperature).filter(v => v !== null));
  sparkHum.seed(sensorHistory.map(r => r.humidity).filter(v => v !== null));
  sparkPress.seed(sensorHistory.map(r => r.pressure).filter(v => v !== null));

  renderMotionTimeline(motionHistory);
  renderModeTimeline(modeHistory);
  renderSkillLog(skillLog);
}
```

### Step 9: Motion Timeline rendering

```html
<div class="motion-timeline">
  <div class="timeline-bar">
    <!-- Dots positioned by timestamp, last 30 minutes -->
  </div>
  <span class="timeline-label">30 min</span>
</div>
```

CSS using xai-DESIGN.md tokens (NOT hardcoded hex):
```css
.motion-timeline { position: relative; height: 24px; background: var(--bg-deep); border-radius: 4px; border: 1px solid rgba(255,255,255,0.06); }
.motion-dot { position: absolute; top: 6px; width: 6px; height: 6px; border-radius: 50%; background: hsl(40, 90%, 50%); }
.timeline-label { position: absolute; right: 4px; bottom: 2px; font-size: 10px; color: var(--text-secondary); font-family: var(--font-mono); }
```

### Step 10: Mode Timeline rendering

```javascript
function renderModeTimeline(intervals) {
  const container = document.getElementById('mode-timeline');
  const now = Date.now();
  const windowMs = 30 * 60 * 1000; // 30 minutes
  const start = now - windowMs;

  let html = '<div class="mode-timeline-bar">';
  for (const interval of intervals) {
    const left = Math.max(0, ((interval.startTime - start) / windowMs) * 100);
    const right = Math.min(100, (((interval.endTime ?? now) - start) / windowMs) * 100);
    const width = right - left;
    html += ``;
  }
  html += '</div>';
  container.innerHTML = html;
}
```

```css
.mode-timeline-bar { position: relative; height: 24px; background: var(--bg-deep); border-radius: 4px; border: 1px solid rgba(255,255,255,0.06); }
.mode-block { position: absolute; top: 2px; bottom: 2px; border-radius: 2px; opacity: 0.7; }
.mode-sleep { background: hsl(240, 60%, 55%); }
.mode-listen { background: hsl(160, 60%, 45%); }
.mode-active { background: hsl(40, 90%, 50%); }
.mode-record { background: hsl(0, 70%, 55%); }
```

### Step 11: DOM Performance — Batched Updates

```javascript
let pendingUpdates = [];
let updateScheduled = false;

function scheduleUpdate(fn) {
  pendingUpdates.push(fn);
  if (!updateScheduled) {
    updateScheduled = true;
    requestAnimationFrame(() => {
      const fragment = document.createDocumentFragment();
      pendingUpdates.forEach(u => u(fragment));
      pendingUpdates = [];
      updateScheduled = false;
      document.getElementById('skill-log').prepend(fragment);
    });
  }
}
```

## Files Changed

| File | Action | Description |
|---|---|---|
| `harness/src/engine/SensorHistory.ts` | NEW | Ring buffer class for sensor history |
| `harness/src/engine/MotionHistory.ts` | NEW | Ring buffer for PIR motion events (Expansion 5.4) |
| `harness/src/engine/ModeHistory.ts` | NEW | Ring buffer for mode transition intervals (Expansion 5.5) |
| `harness/src/core.ts` | MODIFY | Wire SensorHistory, MotionHistory, ModeHistory; add endpoints |
| `harness/src/comms/ControlServer.ts` | MODIFY | Add motion-history and mode-history endpoints, update deps |
| `harness/public/js/telemetry.js` | NEW | TelemetryPanel class, Sparkline (retina DPI), motion/mode timelines |

## Verification

1. Temperature sparkline shows last 5 minutes of data on first load
2. Sparkline updates smoothly with retina DPI support (no blurry on HiDPI)
3. Sparkline flat-line centers vertically when all values are identical
4. Motion timeline shows PIR events as dots in last 30 minutes
5. Skill fire log shows entries in reverse chronological order
6. Escalation events appear with color coding; context shown in collapsible details
7. Conflict events show which skills conflicted and the resolution
8. Mode timeline shows color-coded blocks per mode transition
9. SSE reconnection → sparkline data re-seeded from REST
10. Dashboard remains responsive with 50 skill fires per second (batched DOM updates)
11. `SensorHistory` ring buffer stores max 300 entries, throttled to 1 entry/second
12. `MotionHistory` stores max 180 entries (30 min window)
13. `ModeHistory` stores max 100 intervals, returns open-ended current interval
14. All colors use xai-DESIGN.md tokens (no hardcoded hex)

## Edge Cases

- **MotionHistory empty on first load:** No dots shown, timeline bar is empty. Acceptable.
- **ModeHistory empty on first load:** No blocks shown. If `modeManager.getMode()` returns a mode, seed one interval from boot time.
- **Canvas DPI resize:** If browser window resizes, canvas needs DPI recalculation. Add `window.addEventListener('resize', ...)` to re-setup DPI. Debounce at 200ms.
- **Sparkline with null values:** Sensor readings can be `null` (sensor not yet reported). Filter nulls before passing to sparkline. If all nulls, show "No data" label.

---
*Plan: 08-05 | Phase: 8 | Wave: 2 (frontend) | Depends: 08-01, 08-02*
