daviddatuX25/Xentient/.planning/phases/05-doc-architecture-refactor/05-02-PLAN.md

---
phase: 05-doc-architecture-refactor
plan: 02
type: execute
wave: 2
depends_on: ["05-01"]
files_modified:
  - docs/CONTRACTS.md
  - docs/PACKS.md
  - docs/SPACES.md
  - docs/WEB_CONTROL.md
  - docs/INTEGRATIONS/hermes.md
  - docs/INTEGRATIONS/mem0.md
  - docs/INTEGRATIONS/openclaw.md
autonomous: true
requirements:
  - DOC-02

must_haves:
  truths:
    - "CONTRACTS.md is the authoritative wire format source with Zod schemas, MQTT topic map, message shapes, version field, and 3KB cap"
    - "PACKS.md defines folder spec, manifest schema, handler enum, lifecycle, hot-reload, and junior-dev guardrails"
    - "SPACES.md defines Space model, Mode state machine, integration tiers, and Mem0 scoping"
    - "INTEGRATIONS/hermes.md defines adapter contract, API surface, deployment, and fallback behavior"
    - "INTEGRATIONS/mem0.md defines Mem0 wiring, space-scoped tags, and direct API fallback"
    - "INTEGRATIONS/openclaw.md defines sidecar process manager and sandbox contract"
  artifacts:
    - path: "docs/CONTRACTS.md"
      provides: "Wire format specification, MQTT topics, message schemas"
      min_lines: 60
    - path: "docs/PACKS.md"
      provides: "Pack folder spec, manifest schema, handler enum, lifecycle"
      min_lines: 80
    - path: "docs/SPACES.md"
      provides: "Space model, Mode state machine, integration tiers, Mem0 scoping"
      min_lines: 60
    - path: "docs/INTEGRATIONS/hermes.md"
      provides: "Hermes adapter contract, API surface, deployment"
      min_lines: 40
    - path: "docs/INTEGRATIONS/mem0.md"
      provides: "Mem0 wiring, space-scoped tags, fallback"
      min_lines: 40
    - path: "docs/INTEGRATIONS/openclaw.md"
      provides: "OpenClaw sidecar process manager, sandbox contract"
      min_lines: 30
  key_links:
    - from: "docs/CONTRACTS.md"
      to: "docs/VISION.md"
      via: "architecture diagram reference"
      pattern: "bridge model|integration tier"
    - from: "docs/PACKS.md"
      to: "docs/CONTRACTS.md"
      via: "manifest schema references contracts.ts types"
      pattern: "manifest\.json|contracts"
    - from: "docs/SPACES.md"
      to: "docs/VISION.md"
      via: "Space interface and Mode state machine"
      pattern: "Space\b|SpaceMode|sleep.*listen.*active"
---

<objective>
Create all L2 spec documents: CONTRACTS.md (wire format source of truth), PACKS.md (pack folder spec), SPACES.md (Space model and Modes), and three integration docs (hermes, mem0, openclaw). These specs are the implementation-ready references that a junior developer could code against.

Purpose: These L2 specs are the bridge between vision and implementation. They extract and formalize content currently scattered across NOTES.md and repurpose.md into structured, referenceable documents.

Output: docs/CONTRACTS.md, docs/PACKS.md, docs/SPACES.md, docs/INTEGRATIONS/hermes.md, docs/INTEGRATIONS/mem0.md, docs/INTEGRATIONS/openclaw.md
</objective>

<execution_context>
@$HOME/.claude/get-shit-done/workflows/execute-plan.md
@$HOME/.claude/get-shit-done/templates/summary.md
</execution_context>

<context>
@.planning/phases/05-doc-architecture-refactor/05-CONTEXT.md
@.planning/phases/05-doc-architecture-refactor/05-RESEARCH.md
@docs/repurpose.md
@NOTES.md
@docs/VISION.md (created in 05-01-PLAN)
@docs/NON_GOALS.md (created in 05-01-PLAN)
@docs/HARDWARE.md (created in 05-01-PLAN)

<interfaces>
From NOTES.md (source for contracts and packs):
- B2: Data Contract — Zod schemas, camelCase, epoch-millis uint32, v:1 field, 3KB cap, peripheral ID registry (0x10=Speaker, 0x11=PIR, 0x12=BME280, 0x13=INMP441, 0x14=ESP32-CAM, 0x15=LCD)
- B7: LCD Display — display_update message type: {v:1, type:"display_update", mode:"expression"|"text"|"status", line1:string, line2:string, duration?:ms}
- Pack system: manifest.json schema, persona.md structure, tools.json handler enum, memory-rules.json, voice.json, lifecycle (boot/validate/load/hot-reload/switch), MQTT control topics (xentient/control/pack, xentient/status/packs)
- Pack guardrails: kebab-case names, no path traversal, 1MB asset limit, reserved "default" pack, one pack active at a time

From repurpose.md (source for Spaces and Integrations):
- Space interface: id, nodeBaseId, activePack, mode (SpaceMode), integrations[], role, sensors[]
- SpaceMode type: sleep | listen | active | record
- Integration type union: basic | hermes | hermes+mem0 | openclaw | archon
- Mode transitions: SLEEP→LISTEN (PIR/wake), LISTEN→ACTIVE (user speaks), LISTEN→RECORD (record cmd), ACTIVE→SLEEP (idle timeout/sleep cmd), RECORD→SLEEP (sleep cmd)
- Brain Router handler table: mqtt-publish, mqtt-request-response, basic-llm, hermes-chat, hermes-memory, hermes-skill, computer-use, agent-delegate
- Space + MQTT contract: space_status, space_switch, mode_set, role_set, integration_enable
- Mem0 multi-level scoping: space_id, user_id, role tags, global facts
- Hermes: process-based, REST+WebSocket, 18+ providers, 3-layer memory, 118 skills, Home Assistant
- OpenClaw: Docker sidecar, sandbox execution, screen capture
</interfaces>
</context>

<tasks>

<task type="auto" tdd="false">
  <name>Task 1: Create CONTRACTS.md and PACKS.md</name>
  <files>docs/CONTRACTS.md, docs/PACKS.md</files>
  <read_first>
    NOTES.md
    docs/repurpose.md
    .planning/phases/05-doc-architecture-refactor/05-CONTEXT.md
  </read_first>
  <action>Create two L2 spec documents:

**docs/CONTRACTS.md** — Authoritative wire format source (per D24):

1. Header: "# Xentient Wire Contracts\n\n> L2 Spec — Authoritative source for all message formats, MQTT topics, and data contracts between Node Base, Harness, and integrations. If contracts.ts and this doc disagree, this doc wins until contracts.ts is updated."

2. Section "Versioning" — Every packet has `v: 1` at root level. Harness rejects mismatched versions with `{error:"version_mismatch"}`.

3. Section "Payload Cap" — 3KB hard limit on any MQTT packet. Binary audio over WebSocket has no cap.

4. Section "Key Naming Convention" — camelCase everywhere. ArduinoJson handles both sides.

5. Section "Timestamps" — `epoch-millis uint32` everywhere (half the bytes of ISO8601, demo-safe).

6. Section "Enum Widths" — All opcodes pinned to `uint8_t` (0-255). TS mirrors with `z.number().int().min(0).max(255)`.

7. Section "Peripheral ID Registry" — Table: 0x10=Speaker, 0x11=PIR, 0x12=BME280, 0x13=INMP441, 0x14=ESP32-CAM, 0x15=LCD.

8. Section "MQTT Topic Map" — Table of all topics:
   - `xentient/audio/in` — audio chunks from mic
   - `xentient/audio/out` — TTS audio to speaker
   - `xentient/sensors/env` — environmental sensor data
   - `xentient/sensors/motion` — PIR motion events
   - `xentient/display` — LCD display commands
   - `xentient/display/faces` — LCD face table for pack
   - `xentient/control/pack` — pack switch/reload commands
   - `xentient/status/packs` — pack status responses
   - `xentient/control/space` — space switch commands
   - `xentient/status/space` — space status responses
   - `xentient/control/mode` — mode set commands
   - `xentient/status/mode` — mode status responses
   - `xentient/pipeline/state` — pipeline state transitions
   - `xentient/session/error` — session errors (recoverable vs fatal)

9. Section "Message Schemas" — JSON examples for each message type:
   - Audio chunk: {v:1, type:"audio_chunk", sessionId, sequence, payload:base64}
   - Display update: {v:1, type:"display_update", mode:"expression"|"text"|"status", line1, line2, duration?:ms}
   - Space status: {v:1, type:"space_status", spaces:[...]}
   - Mode command: {v:1, type:"mode_set", mode:"sleep"|"listen"|"active"|"record"}
   - Pack switch: {v:1, type:"pack_switch", name:"pack-name"}
   - Session error: {v:1, type:"session_error", recoverable:bool, message:string}
   - Sensor data: {v:1, type:"sensor_data", peripheralType:enum, payload:{...}}

10. Section "Zod Schema Convention" — All schemas defined in `harness/src/shared/contracts.ts` using Zod. This doc is the design reference; contracts.ts is the runtime enforcement.

**docs/PACKS.md** — Pack folder spec (per D25, NOTES.md Platform Vision section):

1. Header: "# Xentient Pack System\n\n> L2 Spec — Pack folder specification, manifest schema, handler enum, lifecycle, and guardrails. A pack is a folder that defines a bot's behavior."

2. Section "Concept" — "Behavior is a folder." One pack = one persona + tools + voice + memory rules. Swap the folder, swap the brain.

3. Section "Folder Structure":
   ```
   packs/
     <pack-name>/
       manifest.json       # required — Zod-validated
       persona.md          # required — system prompt + optional LCD face overrides
       tools.json          # optional — tool/function defs + MQTT topic bindings
       memory-rules.json   # optional — fact-extraction + injection policy
       voice.json          # optional — TTS provider + voice ID + speed/pitch
       assets/             # optional — custom LCD bitmap chars, audio cues
   ```

4. Section "Manifest Schema" — Full JSON schema for manifest.json:
   - v, name (kebab-case), displayName, author, version, description, capabilities array, compatibility object (harness version, hardware array), entrypoint object (persona, tools, memory, voice)
   - Copy from NOTES.md manifest.json example.

5. Section "Persona Format" — persona.md structure: YAML front-matter (voice, style, greeting, lcdFaces override table), body = system prompt with {{memory.userName}} and {{sensor.temp}} interpolation.

6. Section "Handler Enum" — Table of all handler types with "What It Does" and "Available When" columns:
   - mqtt-publish, mqtt-request-response, basic-llm, hermes-chat, hermes-memory, hermes-skill, computer-use, agent-delegate
   - Copy from repurpose.md Brain Router table (per D25, D5).

7. Section "tools.json Structure" — Array of tool defs with OpenAI-compatible schema. Each tool has a `handler` field that must be one of the enum values above. Example with mqtt-publish handler.

8. Section "memory-rules.json Structure" — extract, inject, retention fields. Copy from NOTES.md.

9. Section "voice.json Structure" — provider, voiceId, speed, pitch, fallback object. Copy from NOTES.md.

10. Section "Lifecycle" — Boot → Load → Validate → Register. Hot-reload via chokidar with 500ms debounce. MemoryDB preserved across reloads. Pack switch via MQTT. Validate fail falls back to `default` pack.

11. Section "Guardrails" (per D28 and NOTES.md junior-dev guardrails):
   - Pack names: `[a-z0-9-]{1,32}` only, kebab-case
   - No `..` path traversal in manifest paths — loader rejects with PathTraversalError
   - Asset files >1MB rejected
   - `default` pack is reserved and always present
   - One pack active at a time — no stacking, no inheritance, no composition
   - Adding a handler type requires a harness PR — intentional friction

12. Section "MQTT Pack Control" — Topics xentient/control/pack and xentient/status/packs with message schemas (pack_list, pack_switch, pack_reload). Copy from NOTES.md.

13. Section "Demo Packs" (per D19) — Two packs for demo: `default` (current behavior, zero visible change) and `angry-dad-mode` (contrastive persona + voice + LCD overrides). Pack system code does NOT ship before demo — this section documents the spec for post-demo P5.</action>
  <verify>
    grep -c "v:.*1\|version.*field\|3KB" docs/CONTRACTS.md && echo "CONTRACTS: versioning and cap present"
    grep -c "xentient/" docs/CONTRACTS.md && echo "CONTRACTS: MQTT topic map present"
    grep -c "display_update\|space_status\|mode_set\|session_error" docs/CONTRACTS.md && echo "CONTRACTS: message schemas present"
    grep -c "manifest\.json\|handler.*enum\|mqtt-publish\|hermes-chat" docs/PACKS.md && echo "PACKS: manifest and handler spec present"
    grep -c "lifecycle\|hot-reload\|guardrail\|path.*traversal" docs/PACKS.md && echo "PACKS: lifecycle and guardrails present"
    test $(wc -l < docs/CONTRACTS.md) -ge 60 && echo "CONTRACTS: minimum line count met"
    test $(wc -l < docs/PACKS.md) -ge 80 && echo "PACKS: minimum line count met"
  </verify>
  <done>CONTRACTS.md is the authoritative wire format reference with MQTT topics, message schemas, and versioning. PACKS.md defines the complete pack system spec with folder structure, manifest schema, handler enum, lifecycle, and guardrails.</done>
</task>

<task type="auto" tdd="false">
  <name>Task 2: Create SPACES.md and INTEGRATIONS directory</name>
  <files>docs/SPACES.md, docs/INTEGRATIONS/hermes.md, docs/INTEGRATIONS/mem0.md, docs/INTEGRATIONS/openclaw.md</files>
  <read_first>
    docs/repurpose.md
    .planning/phases/05-doc-architecture-refactor/05-CONTEXT.md
    NOTES.md
  </read_first>
  <action>Create four documents:

**docs/SPACES.md** — Space model, Mode state machine, integration tiers, Mem0 scoping (per D3, D4, D26):

1. Header: "# Xentient Spaces & Modes\n\n> L2 Spec — Space model, Mode state machine, integration tiers, and memory scoping. Referenced by VISION.md and implemented by SpaceManager/ModeManager in Platform Track P3-P4."

2. Section "What is a Space?" — A Space is an identity context. Space = Identity + Pack + Mode + Permissions + Memory Scope. Like a user account on a computer.

3. Section "Space Interface" — TypeScript interface from repurpose.md:
   ```typescript
   interface Space {
     id: string;                // kebab-case
     nodeBaseId: string;        // MQTT node ID
     activePack: string;        // which pack is loaded
     mode: SpaceMode;           // current operational mode
     integrations: Integration[];// which AI brains are available
     role?: string;             // optional context
     sensors: string[];         // available peripherals
   }
   ```

4. Section "SpaceMode Type" — TypeScript union: "sleep" | "listen" | "active" | "record"

5. Section "Integration Type" — TypeScript union: "basic" | "hermes" | "hermes+mem0" | "openclaw" | "archon"

6. Section "Mode State Machine" — ASCII transition diagram from repurpose.md (SLEEP→LISTEN on PIR/wake, LISTEN→ACTIVE on user speaks, LISTEN→RECORD on record cmd, ACTIVE→SLEEP on idle timeout, RECORD→SLEEP on sleep cmd). Describe each mode's behavior:
   - SLEEP: PIR interrupts only, no STT/TTS, LCD shows (_ _) Zzz
   - LISTEN: VAD active, wake word detection, no LLM calls until triggered
   - ACTIVE: Full pipeline (STT→LLM→TTS), all integrations available per Space config
   - RECORD: Audio capture to file, no response, LCD shows (_ _) REC

7. Section "Space Examples" — Table from repurpose.md: living-room, study-desk, workshop, bedroom with their packs, modes, integrations, roles.

8. Section "Memory Scoping (via Mem0)" — 4-level scoping model:
   - Space-scoped facts: `space_id` tag — "living-room temperature is usually 24C"
   - User-scoped facts: `user_id` tag — "my name is David" (shared across spaces)
   - Role-scoped facts: `role` tag — "I'm studying for midterms" (activates in study-desk space)
   - Global facts: no tag — "Philippines uses 220V outlets"

9. Section "Space + MQTT Contract" — space_status, space_switch, mode_set, role_set, integration_enable message schemas.

10. Section "Platform Track Mapping" — P3 (Mode Manager), P4 (Space Manager) are the implementation phases.

**docs/INTEGRATIONS/hermes.md** — Hermes adapter contract (per D31):

1. Header: "# Hermes Agent Integration\n\n> L2 Spec — Adapter contract for connecting Xentient to a Hermes Agent instance. Implemented in Platform Track P1."

2. Section "What Hermes Provides" — Bullet list from repurpose.md: LLM routing (18+ providers), 3-layer memory, Mem0 as plugin, 118 bundled skills, Home Assistant integration, voice mode, subagent delegation, cron scheduling, 15+ messaging platforms, MCP integration.

3. Section "How Xentient Connects" — HermesAdapter sends text/audio via Hermes API. Hermes handles LLM calls, memory, skills, tool dispatch. Xentient receives responses and routes through voice pipeline or LCD.

4. Section "API Surface" — REST endpoint for tool calls, WebSocket for streaming. Xentient adapter uses WebSocket for streaming, REST for tool calls.

5. Section "Deployment" — Hermes runs as a process on server (local or cloud). Xentient doesn't care where brain runs — just needs connection.

6. Section "Fallback Behavior" — When Hermes is unavailable, Xentient falls back to basic mode (direct LLM provider call, no memory, no skills). Terminal never bricks because brain is offline.

7. Section "What It Replaces" — memory/MemoryDB.ts → DELETE, memory/FactExtractor.ts → DELETE, memory/MemoryInjector.ts → DELETE, memory/schema.ts → DELETE. ~300 LOC custom code replaced by ~80 LOC adapter.

8. Section "Platform Track Mapping" — P1 (Hermes Adapter) is the implementation phase.

**docs/INTEGRATIONS/mem0.md** — Mem0 wiring and fallback (per D32):

1. Header: "# Mem0 Integration\n\n> L2 Spec — Mem0 as primary memory layer with direct API fallback for basic mode. Implemented in Platform Track P2."

2. Section "What Mem0 Provides" — Semantic memory, recency weighting, entity resolution, multi-level scoping (maps to Spaces), graph memory, search, versioning.

3. Section "Primary Path" — Hermes plugin. When Hermes is active, Mem0 is a first-class Hermes plugin. `hermes memory setup` → select Mem0 → done.

4. Section "Fallback Path" — Mem0Adapter (direct API). When Hermes is not available but memory is still desired, Xentient calls Mem0 API directly. This enables "basic mode with memory" without the full Hermes runtime.

5. Section "Space-Scoped Tags" — How Mem0 multi-level scoping maps to Xentient Spaces: space_id, user_id, role tags. Every Mem0 call includes context tags matching the active Space.

6. Section "What It Replaces" — Same as Hermes doc: MemoryDB/FactExtractor/MemoryInjector/schema → DELETE. Mem0 provides all of this production-grade.

7. Section "Deployment" — Self-hosted Docker (recommended for privacy) or cloud API. Both supported by architecture.

8. Section "Platform Track Mapping" — P2 (Mem0 Integration) is the implementation phase.

**docs/INTEGRATIONS/openclaw.md** — OpenClaw sidecar contract (per D33):

1. Header: "# OpenClaw Integration\n\n> L2 Spec — OpenClaw as a computer-use sidecar for terminal, browser, and filesystem operations. Implemented in Platform Track P7."

2. Section "What OpenClaw Provides" — Battle-tested computer-use agent with sandbox execution, screen capture, terminal access, browser control.

3. Section "How Xentient Connects" — OpenClawAdapter sends instructions via API. Results come back as text/structured data. Always sandboxed — Xentient cannot bypass OpenClaw's isolation.

4. Section "Sidecar Architecture" — OpenClaw runs as Docker container. Xentient's adapter manages the sidecar lifecycle: start, health check, send instruction, receive result, timeout handling.

5. Section "Security Model" — computer-use handler always runs in OpenClaw's sandbox. Xentient can't bypass isolation. Space permissions gate availability: `study-desk` can't use computer-use unless configured.

6. Section "Platform Track Mapping" — **P8 (OpenClaw Adapter)** is the implementation phase per the updated Platform Track P1-P9 ordering (P6=Web Control Panel, P7=Communication Bridge, P8=OpenClaw, P9=Archon). This supersedes any earlier P6/P7 labels in repurpose.md or CONTEXT.md — the authoritative order is defined in docs/VISION.md migration table and .planning/ROADMAP.md Platform Track.

</action>
  <verify>
    grep -c "Space\b.*interface\|SpaceMode\|sleep.*listen.*active.*record" docs/SPACES.md && echo "SPACES: model and modes present"
    grep -c "Mem0\|space_id\|user_id.*role\|scoping" docs/SPACES.md && echo "SPACES: Mem0 scoping present"
    grep -c "HermesAdapter\|fallback\|basic mode" docs/INTEGRATIONS/hermes.md && echo "HERMES: adapter and fallback present"
    grep -c "memory.*DELETE\|300 LOC\|80 LOC" docs/INTEGRATIONS/hermes.md && echo "HERMES: replacement scope present"
    grep -c "Mem0Adapter\|direct API\|fallback\|space_id" docs/INTEGRATIONS/mem0.md && echo "MEM0: adapter and scoping present"
    grep -c "sandbox\|OpenClawAdapter\|sidecar\|Docker" docs/INTEGRATIONS/openclaw.md && echo "OPENCLAW: sidecar and sandbox present"
    test $(wc -l < docs/SPACES.md) -ge 60 && echo "SPACES: minimum line count met"
    test $(wc -l < docs/INTEGRATIONS/hermes.md) -ge 40 && echo "HERMES: minimum line count met"
    test $(wc -l < docs/INTEGRATIONS/mem0.md) -ge 40 && echo "MEM0: minimum line count met"
    test $(wc -l < docs/INTEGRATIONS/openclaw.md) -ge 30 && echo "OPENCLAW: minimum line count met"
  </verify>
  <done>SPACES.md defines Space model, Mode state machine, integration tiers, and Mem0 scoping. Three integration docs define adapter contracts for Hermes, Mem0, and OpenClaw with implementation phase mappings.</done>
</task>

<task type="auto" tdd="false">
  <name>Task 3: Create WEB_CONTROL.md (Core's Face B spec)</name>
  <files>docs/WEB_CONTROL.md</files>
  <read_first>
    docs/repurpose.md
    .planning/phases/05-doc-architecture-refactor/05-CONTEXT.md
  </read_first>
  <action>Create docs/WEB_CONTROL.md as the L2 spec for the Web Control Panel — Face B of the Core (Face A = Runtime daemon, same codebase, always-on host):

1. Header: "# Xentient Web Control Panel\n\n> L2 Spec — Core's Face B. Browser-based control plane for hardware configuration, state management, pack/space permissions, and integration toggles. Shares the Core codebase with the Runtime daemon. Implemented in Platform Track P6."

2. Section "Role in the Three-Tier Architecture" — Tier 1 (Hardware) ↔ Tier 2 (Core = Runtime + Web Control Panel) ↔ Tier 3 (AI Brain). The Web Control Panel is the human-facing surface of Core. Runtime is the machine-facing surface. Both read/write the same Core state (MQTT broker, Space registry, Pack registry, Brain Router config).

3. Section "Hosting Model" — Core runs live 24/7 on a server (self-hosted or cloud VPS). Web Control Panel is served from the same process or a sibling process on the same host. Node Bases connect to Core over MQTT/WebSocket. Admin users connect to Web Control Panel over HTTPS.

4. Section "Core Responsibilities" — what Web Control Panel lets the operator do:
   - Hardware config: register Node Bases, assign peripheral IDs (0x10-0x15 per CONTRACTS.md), view live telemetry
   - Space management: create/edit Spaces (id, nodeBaseId, activePack, mode, integrations, role, sensors)
   - Mode control: force sleep/listen/active/record on any Space (override state machine)
   - Pack management: list installed packs, switch active pack per Space, hot-reload, upload new pack folder
   - Permissions: which Spaces can call which integration tiers (basic / hermes / hermes+mem0 / openclaw / archon)
   - Integration toggles: enable/disable Hermes, Mem0, OpenClaw, Archon per Space
   - Live telemetry: current mode, active pack, last utterance, sensor readings, brain tier in use
   - Audit log: who changed what and when

5. Section "API Surface" — REST for config reads/writes, WebSocket for live telemetry streaming. All endpoints authenticated (session-based). API calls translate to MQTT control messages (xentient/control/pack, xentient/control/space, xentient/control/mode) — Web Control Panel is a client of the same contracts documented in CONTRACTS.md.

6. Section "Tech Stack Note" — No framework locked in yet. Defer decision to P6 planning. Constraint: must run alongside Runtime daemon on same host without blocking MQTT/voice pipeline event loop.

7. Section "Demo Scope" — Web Control Panel does NOT ship in Apr 24 demo (per D17). This spec documents the post-demo target.

8. Section "Platform Track Mapping" — P6 (Web Control Panel) is the implementation phase. Depends on P3 (Mode Manager) and P4 (Space Manager) — needs their state to display/control.</action>
  <verify>
    grep -c "Web Control Panel\|Face B\|Core.*Runtime" docs/WEB_CONTROL.md && echo "WEB_CONTROL: Core-Face-B framing present"
    grep -c "hardware config\|pack management\|permissions\|integration toggles" docs/WEB_CONTROL.md && echo "WEB_CONTROL: responsibilities present"
    grep -c "P6\|Platform Track" docs/WEB_CONTROL.md && echo "WEB_CONTROL: phase mapping present"
    test $(wc -l < docs/WEB_CONTROL.md) -ge 40 && echo "WEB_CONTROL: minimum line count met"
  </verify>
  <done>WEB_CONTROL.md defines Core's Face B as the L2 spec for browser-based hardware/pack/space/permission management, mapped to Platform Track P6.</done>
</task>

</tasks>

<threat_model>
## Trust Boundaries

| Boundary | Description |
|---|---|
| Documentation reader → project | No trust boundary — specs are public project artifacts |

## STRIDE Threat Register

| Threat ID | Category | Component | Disposition | Mitigation Plan |
|---|---|---|---|---|
| T-05-03 | Repudiation | CONTRACTS.md | accept | Version field (v:1) provides contract versioning; git tracks changes |
| T-05-04 | Spoofing | PACKS.md guardrails | mitigate | PathTraversalError rejection and 1MB asset limit prevent injection attacks at the spec level |
</threat_model>

<verification>
1. docs/CONTRACTS.md exists with MQTT topic map, message schemas, versioning
2. docs/PACKS.md exists with folder spec, manifest schema, handler enum, guardrails
3. docs/SPACES.md exists with Space model, Mode state machine, Mem0 scoping
4. docs/INTEGRATIONS/hermes.md exists with adapter contract and fallback
5. docs/INTEGRATIONS/mem0.md exists with wiring, scoping, and fallback
6. docs/INTEGRATIONS/openclaw.md exists with sidecar and sandbox contract
7. All handler types from Brain Router appear in PACKS.md
8. All MQTT topics from VISION.md appear in CONTRACTS.md
</verification>

<success_criteria>
- CONTRACTS.md is the single source of truth for wire formats with complete MQTT topic map
- PACKS.md defines the full pack system spec with manifest schema, handler enum, lifecycle, and guardrails
- SPACES.md defines Space model, Mode transitions, integration tiers, and Mem0 scoping
- Three integration docs define adapter contracts with deployment, fallback, and implementation phase mapping
- All docs cross-reference VISION.md for architecture concepts
</success_criteria>

<output>
After completion, create `.planning/phases/05-doc-architecture-refactor/05-02-SUMMARY.md`
</output>
