daviddatuX25/Xentient/CONTEXT.md

# XENTIENT — Project Context & Direction

> **This is the single authoritative direction document.**
> Read this before touching any code. All other docs are subordinate to this.
> Last updated: 2026-04-30
>
> **Architectural shift (2026-04-30):** Core's operating concept is now `activeConfig` (configuration),
> not `activeMode` (behavioral mode). See `07-REALIGN-PLAN.md` for the full realignment plan.
> NodeSkill → NodeProfile compilation is the two-layer contract model.

---

## The One-Sentence Vision

**Xentient is a physical room that thinks** — a hardware terminal that any AI brain can inhabit, where the room itself is always-on and intelligent, and the AI is a swappable guest.

---

## The Core Insight (What We Are Building)

We are NOT building another AI chatbot. We are building the **body** that AI chatbots run in.

The analogy that matters:
- A **computer** has a CPU (always on), RAM, and apps (programs that run and exit).
- **Xentient Core** is the CPU — always on, always aware, never sleeps fully.
- **Xentient Brain** is the sandbox — where apps (Hermes, Archon, Claude Code) run.

The room is alive. The brain is a guest.

---

## Two Processes. Two Responsibilities. One System.

### CORE — The Always-On Orchestrator

Core is a **process that never stops**. It is the nervous system of the room.

**What Core owns:**
- Hardware bridge (MQTT ↔ ESP32 Node Bases)
- Audio WebSocket server (raw PCM in, TTS PCM out)
- Camera WebSocket server (JPEG frames in, relay to Dashboard)
- The skill heartbeat loop (deterministic, sub-millisecond)
- Mode state machine (sleep → listen → active → record)
- Space manager (which room, which identity, which permissions)
- MCP server (8+ tools — the API surface the Brain connects to)
- ControlServer (16+ REST endpoints — the API surface the Dashboard connects to)
- Observability bus (SSE → Web Dashboard, 10+ event types)
- LCD face state machine
- Artifact writer (audio + transcript + metadata to disk)

**What Core does NOT do:**
- No LLM calls inside Core itself
- No STT/TTS pipeline inside Core itself (this belongs to Brain)
- No memory management (Brain handles memory)
- No reasoning (Brain handles reasoning)

**Core can run anywhere:** A Raspberry Pi, a home server, a VPS. If Core is on a powerful machine, it can ALSO host the Brain sandbox on the same box — but Core and Brain remain separate processes regardless.

---

### BRAIN — The Connected Sandbox

The Brain is not a fixed process. It is a **connected sandbox** — any process that speaks MCP and can receive escalations from Core. The Brain Interface has three channels:

**Channel 1 — Escalation Inbox:** Core pushes escalations here. Audio payloads, sensor snapshots, mode context, the CoreSkill that fired. The Brain receives this and starts working.

**Channel 2 — Stream Out:** The Brain pushes its reasoning stream back to Core via `xentient_brain_stream`. Token by token. Tool calls as they fire. Core forwards these onto the SSE observability bus. The Dashboard renders them live.

**Channel 3 — Tool Calls Back to Core:** The Brain calls `xentient_*` MCP tools to act on the room. Play audio, register skills, change modes, push node skills, write artifacts.

Any process implementing these three channels is a valid Brain. Hermes does all three natively. A simple script could do Channel 1 and 3 only (no streaming). Claude Code could do all three plus computer use. The interface is the contract, not the implementation.

The Brain runs where the power is — a workstation, a VPS, a powerful local server. Its reach is bounded by the machine it runs on. Core intentionally has no reach beyond the room. The Brain has whatever reach its host machine allows.

Hermes is the reference Brain implementation. It implements all three channels fully — memory recall, LLM reasoning, skill execution, and live streaming of its reasoning process back to the Core observability bus.

The **Brain Feed** is the live window into the sandbox — visible in the Web Dashboard alongside Core telemetry. When Core escalates, you see it. When Brain reasons, you see it. When the room responds, you see it.

---
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
