daviddatuX25/Xentient/xentient.md

# Xentient
### A programmable nervous system for intelligent spaces

> *"Any space. Any AI. Any body."*

---

## What Xentient Is

Xentient is the IoT terminal — a thin voice/hardware bridge that lets any AI brain inhabit a physical room. It gives AI ears to hear, eyes to see, and a voice to respond — deployed across spaces that are named, owned, and programmable. The harness is a terminal OS; intelligence plugs in via integration tiers.

It is not a smart speaker. It is not a home automation hub. It is not tied to any single AI vendor.

It is infrastructure. The bridge between raw physical sensing and intelligent response — owned by the user, programmable at every level, and built to outlast any single model or service.

---

## The Name

**Xentient** — from *sentient* (capable of perception and experience) with the prefix *X* marking the unknown, the extensible, the cross-platform nature of the system.

A Xentient space perceives. It remembers. It responds. But what it thinks with — the model, the rules, the personality — is entirely up to whoever builds it.

---

## Core Principles

**1. Hardware is dumb. Intelligence is a choice.**
Nodes sense and actuate. Nothing more. Every decision about what to do with sensed data — when to wake, how to identify, which AI to invoke — lives in software above the hardware layer.

**2. The space is the product.**
Not the device. A space is a named, owned, intelligent environment. Nodes are assigned to spaces. Harnesses run in spaces. Users interact with spaces. The physical world is just the input surface.
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
